fubarino/fubarino.github.com/images/FubarinoMiniLarge.jpg

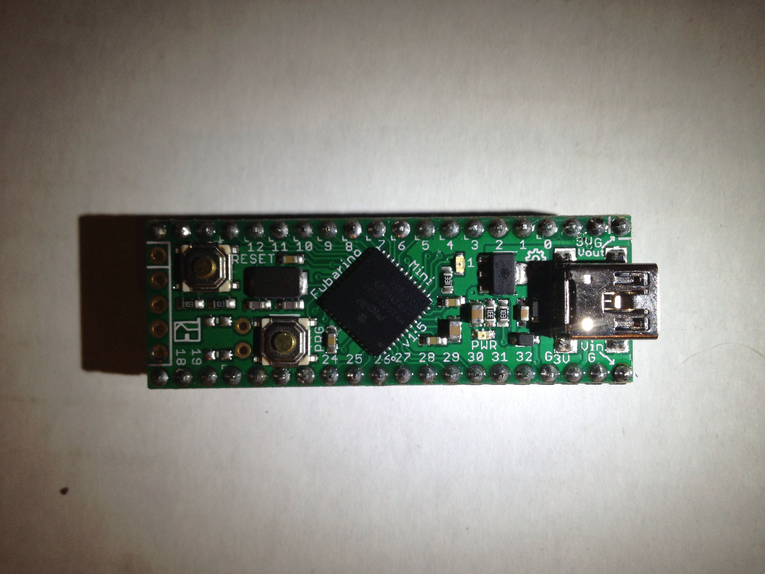
images/FubarinoMiniLarge.jpg
