fubarino/fubarino.github.com/images/FubarinoMiniMCHP.png

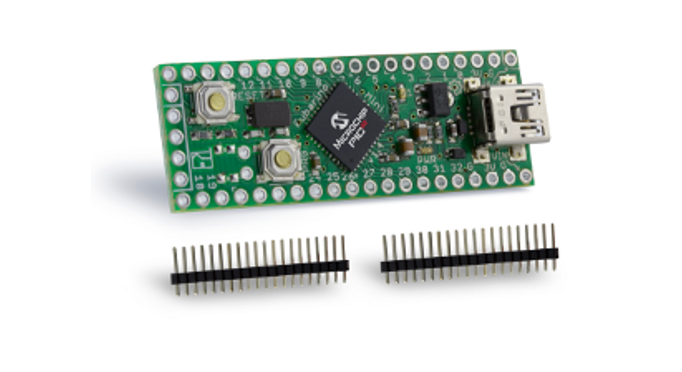
images/FubarinoMiniMCHP.png
