fubarino/fubarino.github.com/images/FubarinoMiniv15-caro-0.jpg

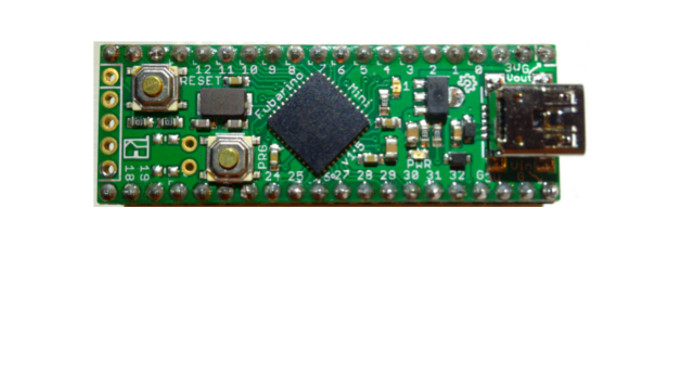
images/FubarinoMiniv15-caro-0.jpg
