fubarino/fubarino.github.com/images/FubarinoMiniv15-caro-1.jpg

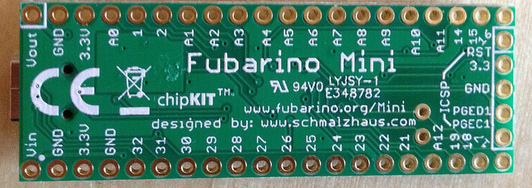
images/FubarinoMiniv15-caro-1.jpg
