fubarino/fubarino.github.com/images/FubarinoMiniv15-small.jpg

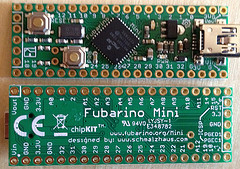
images/FubarinoMiniv15-small.jpg
