fubarino/fubarino.github.com/images/fubarinosd1.jpg

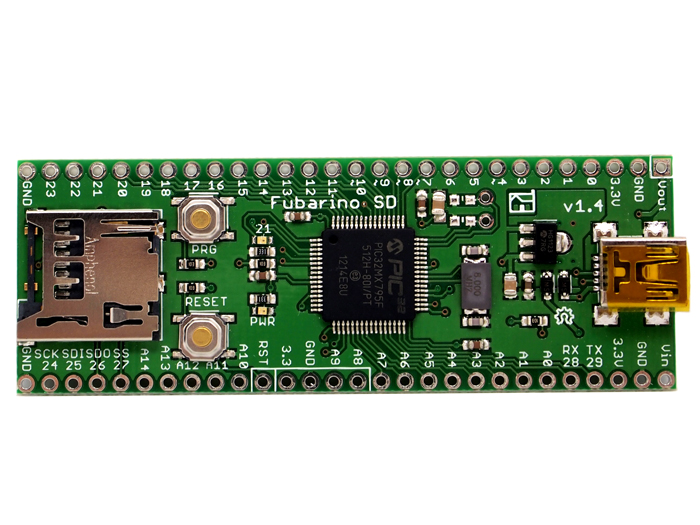
images/fubarinosd1.jpg
