fubarino/fubarino.github.com/images/fubarinosd1.png

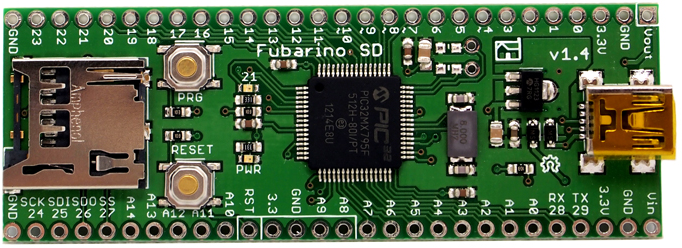
images/fubarinosd1.png
