fubarino/fubarino.github.com/images/fubarinosd2.jpg

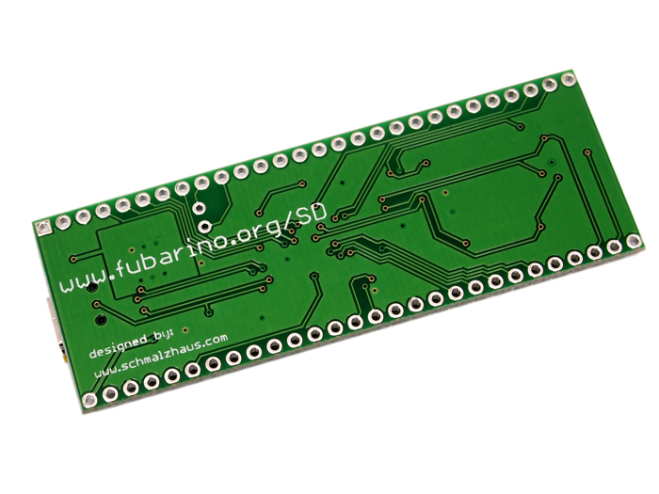
images/fubarinosd2.jpg
