fubarino/fubarino.github.com/images/fubarinosd-caro.jpg

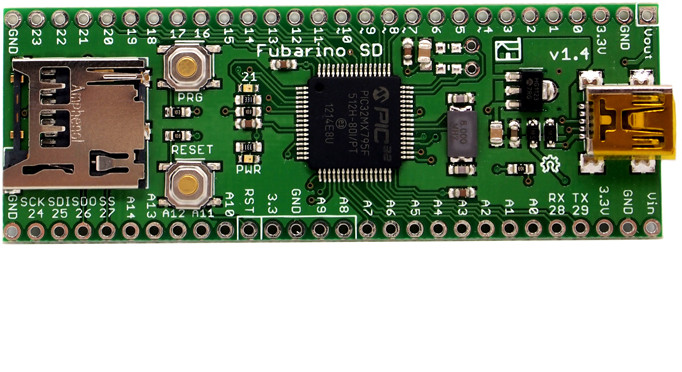
images/fubarinosd-caro.jpg
