fubarino/fubarino.github.com/images/fubarinosd.jpg

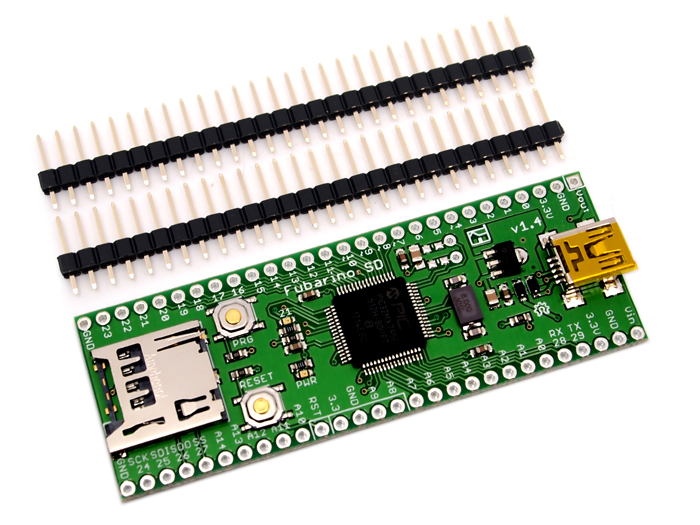
images/fubarinosd.jpg
