fubarino/fubarino.github.com/images/TCHIP011_chipKITFubarinoMini.png

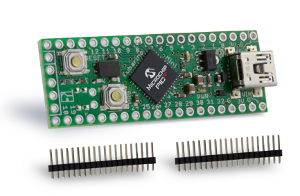
images/TCHIP011_chipKITFubarinoMini.png
