fubarino/fubarino.github.com/mini/docs/FubarinoMini1_5Diagram.png

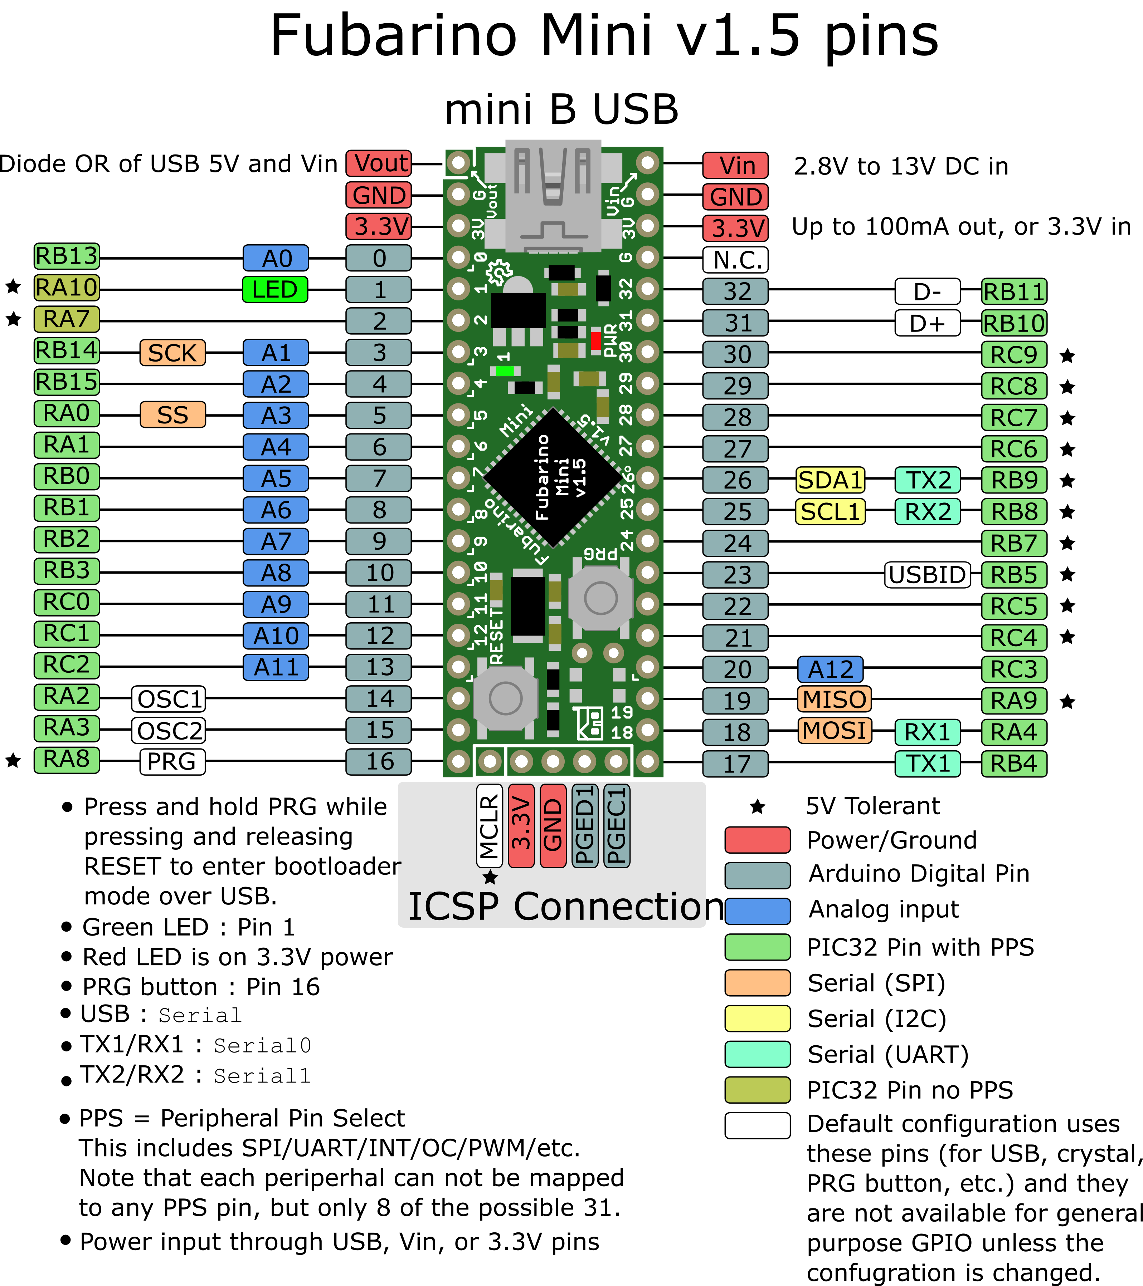
mini/docs/FubarinoMini1_5Diagram.png
