fubarino/fubarino.github.com/mini/fubarinoMini.png

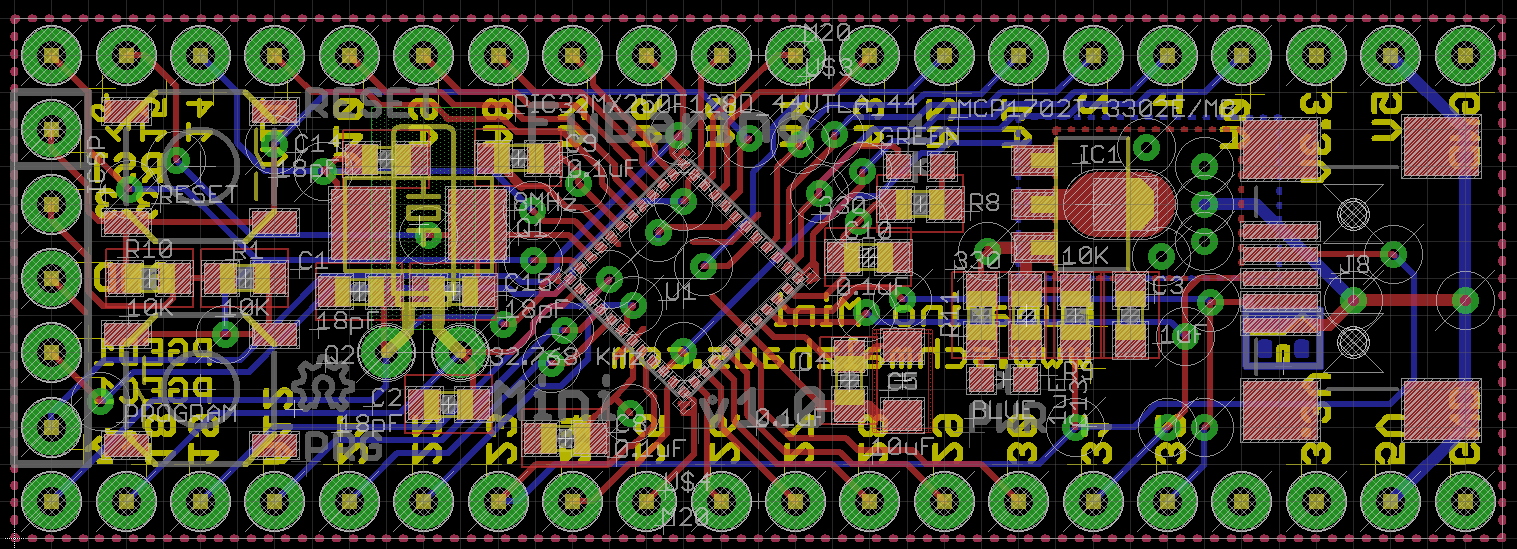
mini/fubarinoMini.png
