fubarino/fubarino.github.com/rawfiles/ProgrammingFubarino.jpg

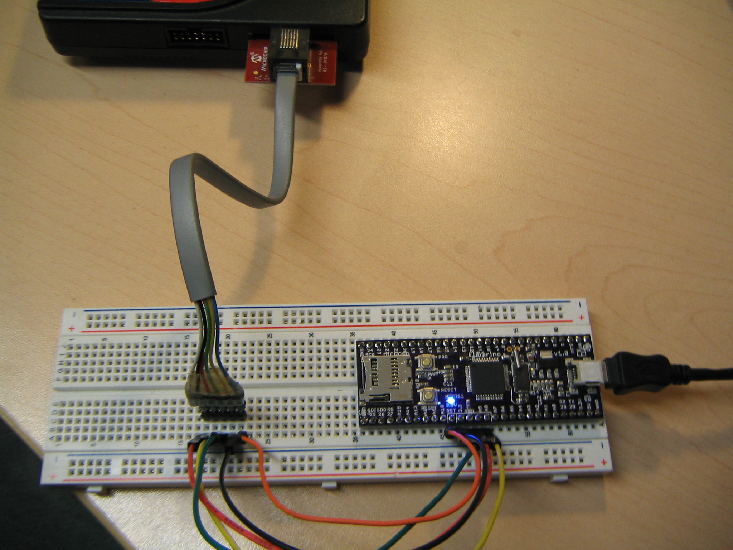
rawfiles/ProgrammingFubarino.jpg
