fubarino/fubarino.github.com/rawfiles/ShieldAdapterMockup.png

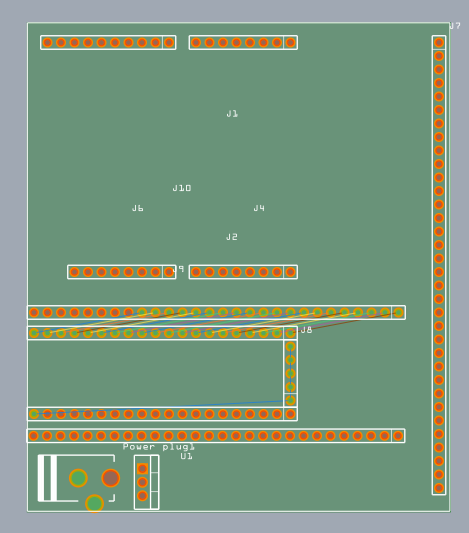
rawfiles/ShieldAdapterMockup.png
