fubarino/fubarino.github.com/rawfiles/shields/AdapterShield.png

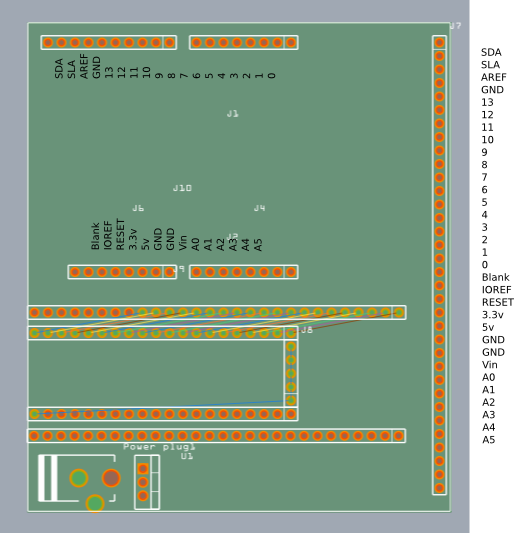
rawfiles/shields/AdapterShield.png
