fubarino/fubarino.github.com/sd/fubarinoSD.png

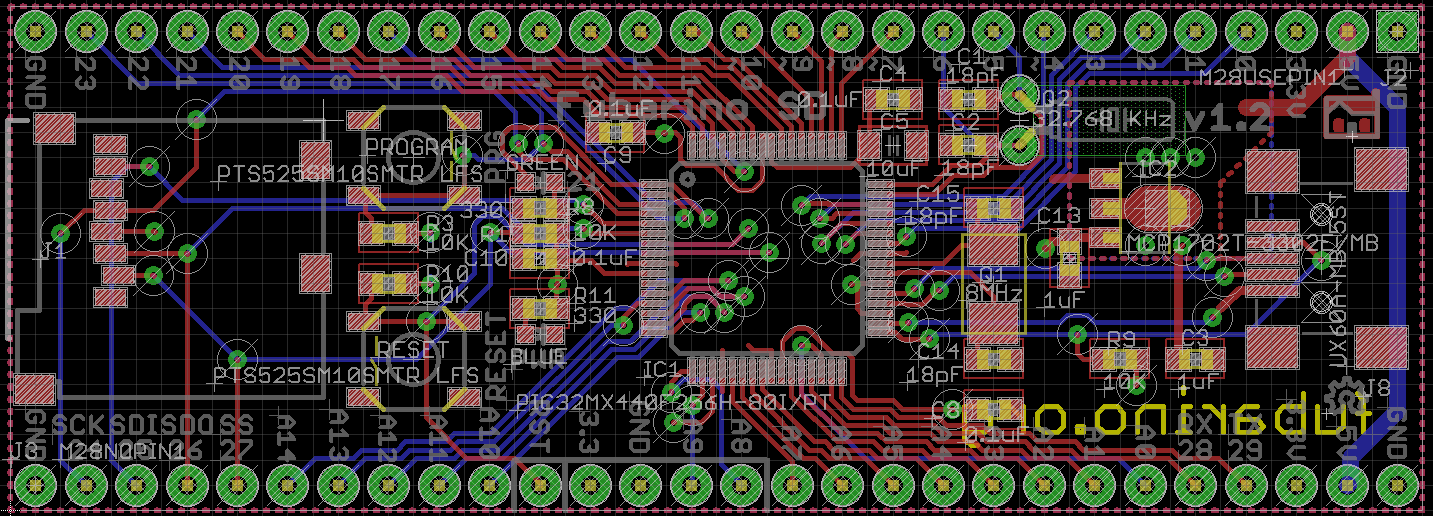
sd/fubarinoSD.png
