fubarino/fubarino.github.com/sd/v1.5/05-10133r15/Fubarino_SD_v15_DRC_screencap.png

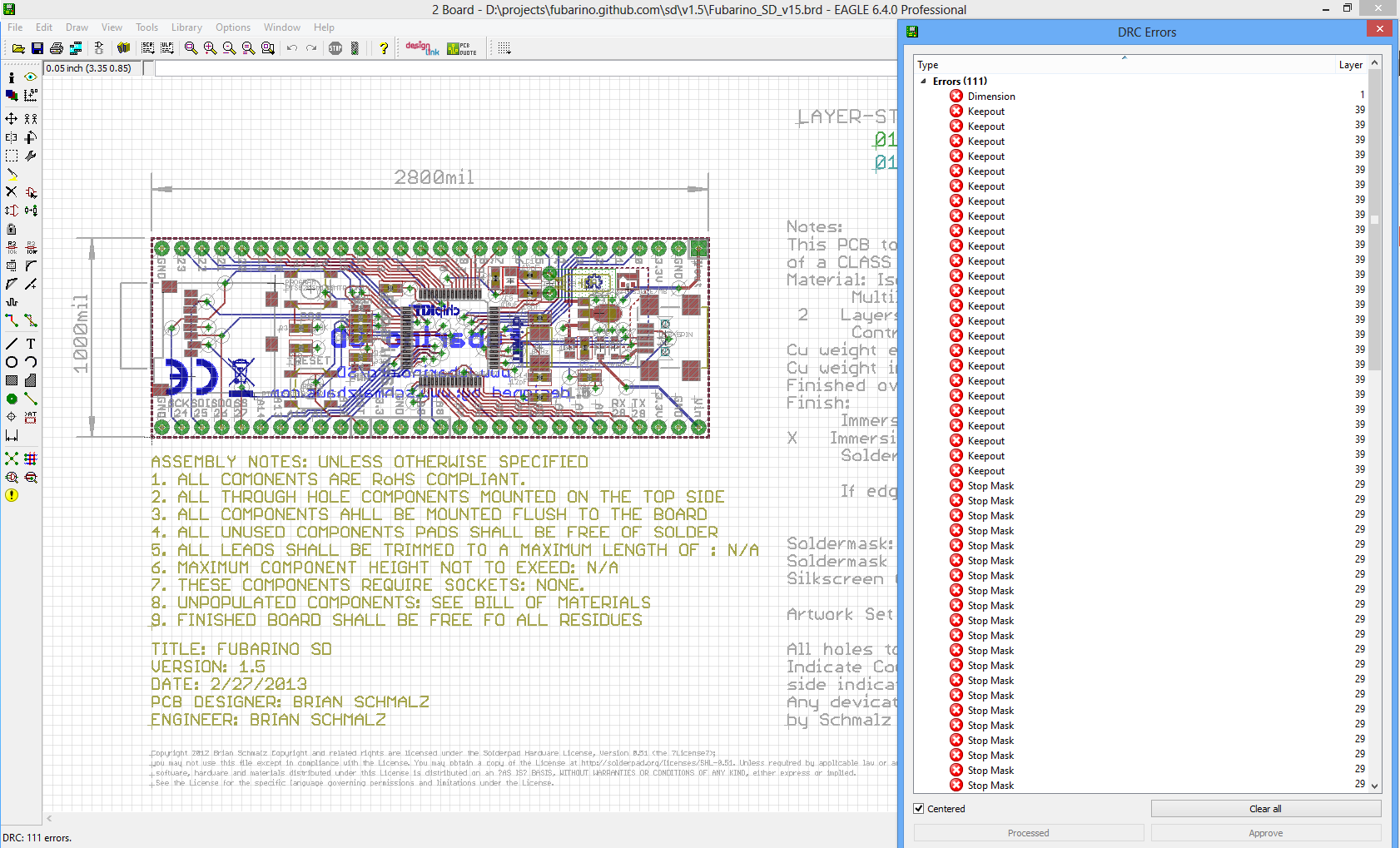
sd/v1.5/05-10133r15/Fubarino_SD_v15_DRC_screencap.png
