fubarino/fubarino.github.com/sd/v1.5/FubarinoSD_bottom_render.png

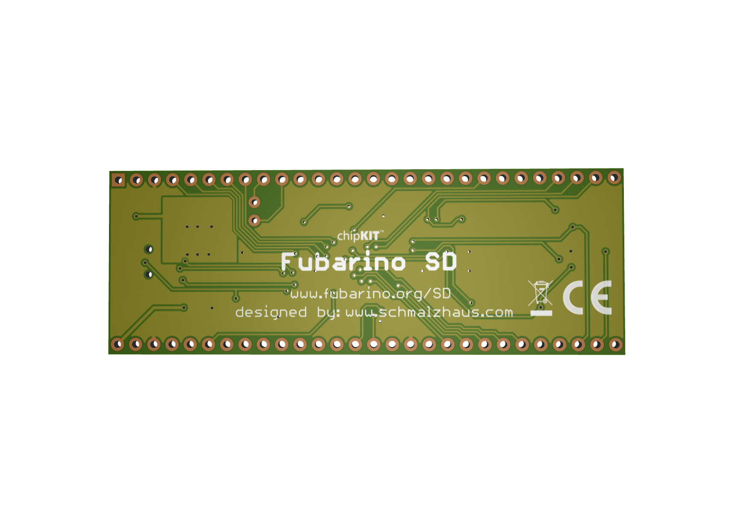
sd/v1.5/FubarinoSD_bottom_render.png
