fubarino/fubarino.github.com/accessories/FubarStep/FuabarStep_v13/FubarStep_v13_brd.png

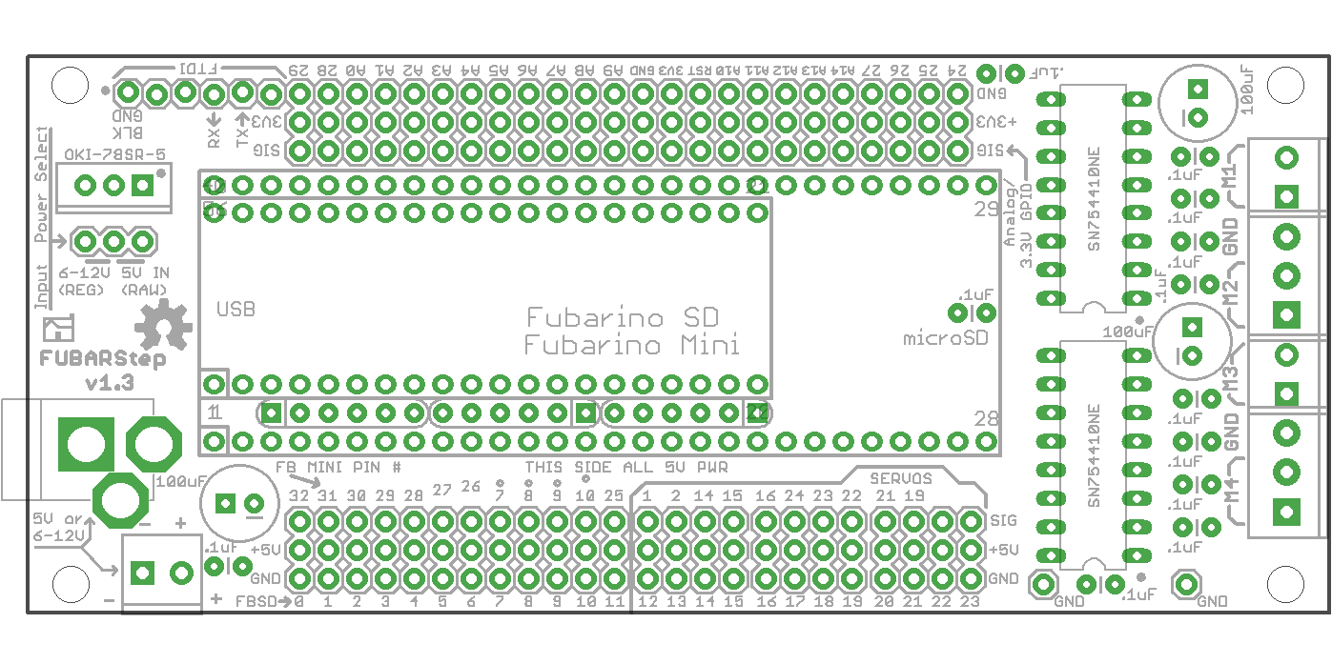
accessories/FubarStep/FuabarStep_v13/FubarStep_v13_brd.png
