fubarino/fubarino.github.com/accessories/FubarStep/FuabarStep_v13/FubarStep_v13_sch.pdf

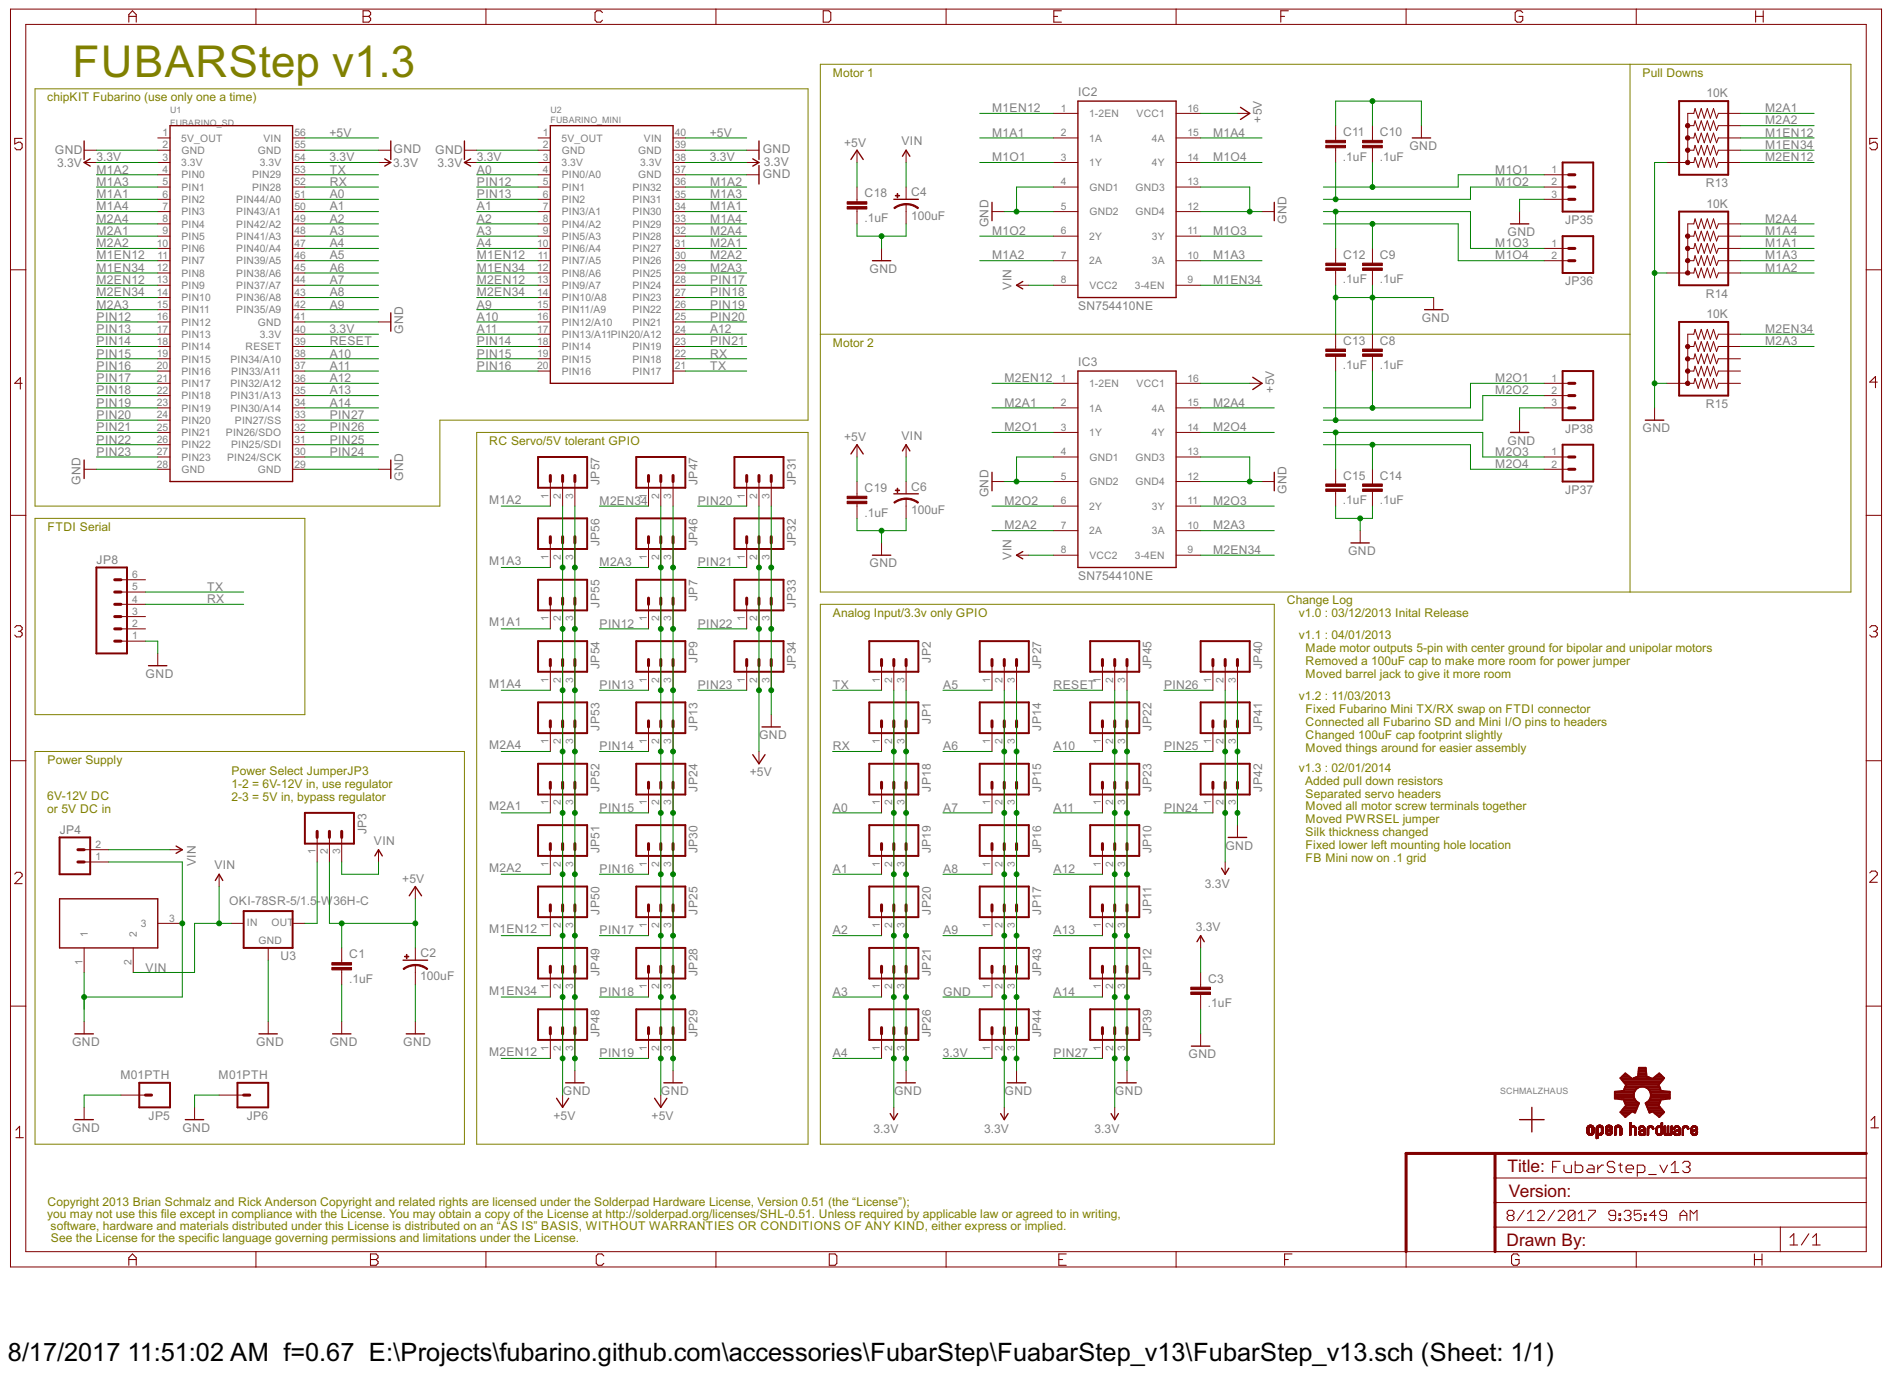
[picture p30: page 1]

chipKIT Fubarino (use only one a time)

RC Servo/5V tolerant GPIO

Analog Input/3.3v only GPIO

v1.1 : 04/01/2013 Made motor outputs 5-pin with center ground for bipolar and unipolar motors Removed a 100uF cap to make more room for power jumper Moved barrel jack to give it more room

v1.2 : 11/03/2013 Fixed Fubarino Mini TX/RX swap on FTDI connector Connected all Fubarino SD and Mini I/O pins to headers Changed 100uF cap footprint slightly Moved things around for easier assembly

Power Select JumperJP3
1-2 = 6V-12V in, use regulator 2-3 = 5V in, bypass regulator

v1.3 : 02/01/2014 Added pull down resistors Separated servo headers Moved all motor screw terminals together Moved PWRSEL jumper Silk thickness changed Fixed lower left mounting hole location FB Mini now on .1 grid

Drawn By: Title: Version:

Copyright 2013 Brian Schmalz and Rick Anderson Copyright and related rights are licensed under the Solderpad Hardware License, Version 0.51 (the “License”); you may not use this file except in compliance with the License. You may obtain a copy of the License at http://solderpad.org/licenses/SHL-0.51. Unless required by applicable law or agreed to in writing, software, hardware and materials distributed under this License is distributed on an “AS IS” BASIS, WITHOUT WARRANTIES OR CONDITIONS OF ANY KIND, either express or implied. See the License for the specific language governing permissions and limitations under the License.

8/17/2017 11:51:02 AM f=0.67 E:\Projects\fubarino.github.com\accessories\FubarStep\FuabarStep_v13\FubarStep_v13.sch (Sheet: 1/1)
