fubarino/fubarino.github.com/mini/v20/02-10134r20-D.pdf

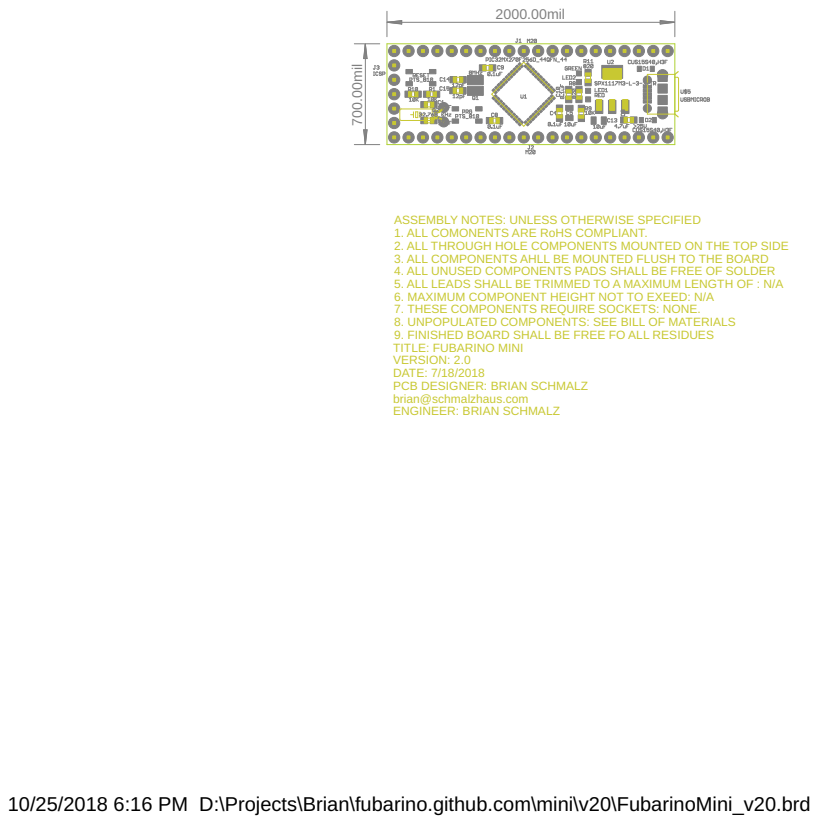
[picture p31: page 1]

ASSEMBLY NOTES: UNLESS OTHERWISE SPECIFIED
1. ALL COMONENTS ARE RoHS COMPLIANT. 2. ALL THROUGH HOLE COMPONENTS MOUNTED ON THE TOP SIDE

3. ALL COMPONENTS AHLL BE MOUNTED FLUSH TO THE BOARD
4. ALL UNUSED COMPONENTS PADS SHALL BE FREE OF SOLDER
5. ALL LEADS SHALL BE TRIMMED TO A MAXIMUM LENGTH OF : N/A
6. MAXIMUM COMPONENT HEIGHT NOT TO EXEED: N/A
7. THESE COMPONENTS REQUIRE SOCKETS: NONE. 8. UNPOPULATED COMPONENTS: SEE BILL OF MATERIALS

9. FINISHED BOARD SHALL BE FREE FO ALL RESIDUES
TITLE: FUBARINO MINI VERSION: 2.0 DATE: 7/18/2018 PCB DESIGNER: BRIAN SCHMALZ

10/25/2018 6:16 PM D:\Projects\Brian\fubarino.github.com\mini\v20\FubarinoMini_v20.brd
