fubarino/fubarino.github.com/mini/v20/04-10134r20.pdf

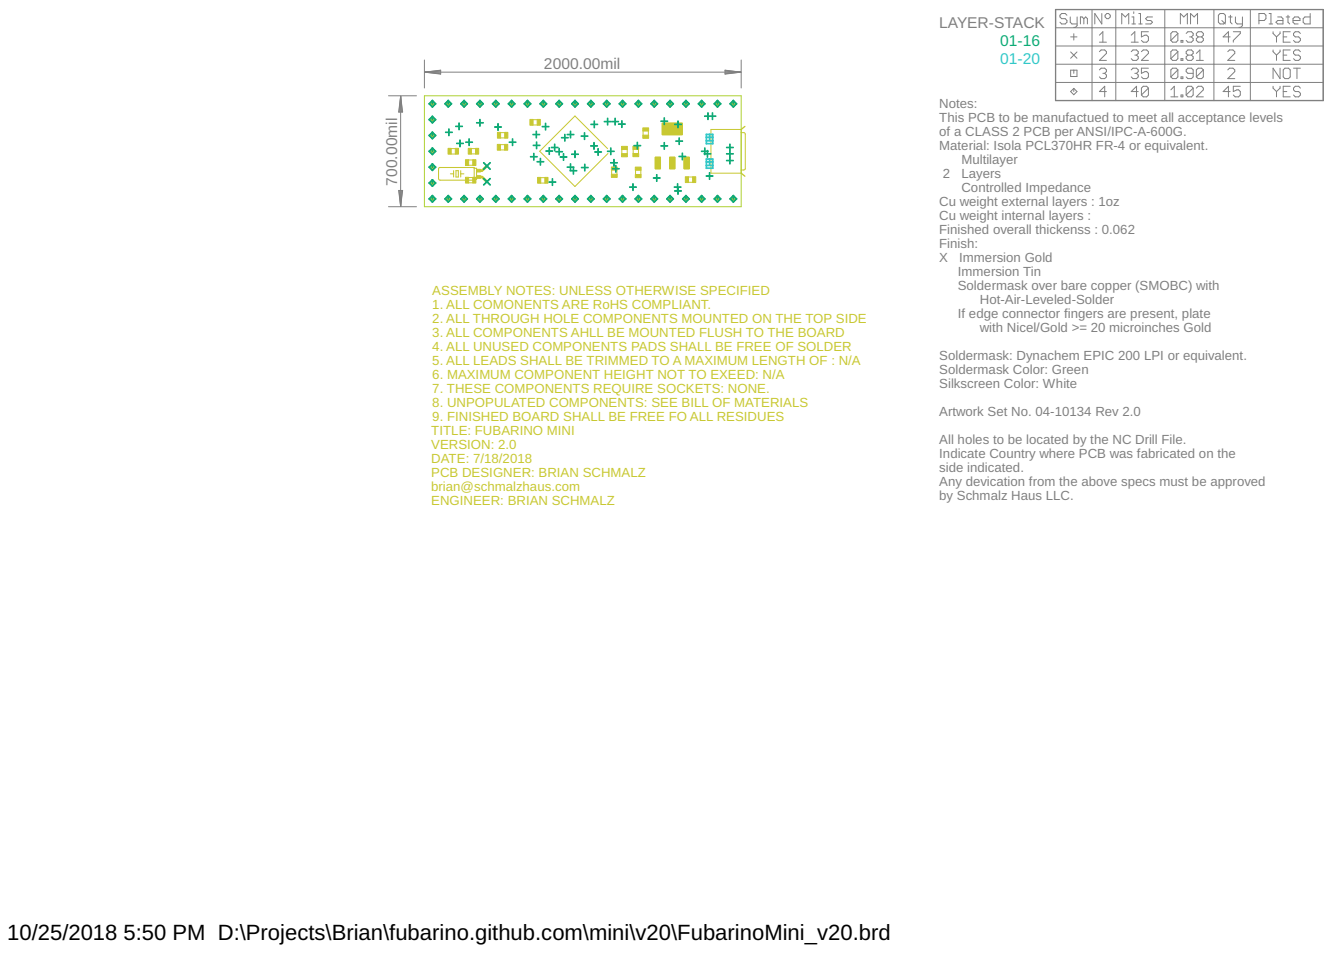
[picture p32: page 1]

01-20 Notes: This PCB to be manufactued to meet all acceptance levels of a CLASS 2 PCB per ANSI/IPC-A-600G. Material: Isola PCL370HR FR-4 or equivalent. Multilayer 2 Layers Controlled Impedance Cu weight external layers : 1oz Cu weight internal layers : Finished overall thickenss : 0.062 Finish: X Immersion Gold

Immersion Tin Soldermask over bare copper (SMOBC) with Hot-Air-Leveled-Solder

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

If edge connector fingers are present, plate with Nicel/Gold >= 20 microinches Gold Soldermask: Dynachem EPIC 200 LPI or equivalent. Soldermask Color: Green Silkscreen Color: White Artwork Set No. 04-10134 Rev 2.0 All holes to be located by the NC Drill File.

3. ALL COMPONENTS AHLL BE MOUNTED FLUSH TO THE BOARD
4. ALL UNUSED COMPONENTS PADS SHALL BE FREE OF SOLDER
5. ALL LEADS SHALL BE TRIMMED TO A MAXIMUM LENGTH OF : N/A
6. MAXIMUM COMPONENT HEIGHT NOT TO EXEED: N/A
7. THESE COMPONENTS REQUIRE SOCKETS: NONE. 8. UNPOPULATED COMPONENTS: SEE BILL OF MATERIALS

9. FINISHED BOARD SHALL BE FREE FO ALL RESIDUES
TITLE: FUBARINO MINI VERSION: 2.0 DATE: 7/18/2018 PCB DESIGNER: BRIAN SCHMALZ

Indicate Country where PCB was fabricated on the
side indicated. Any devication from the above specs must be approved

by Schmalz Haus LLC.

10/25/2018 5:50 PM D:\Projects\Brian\fubarino.github.com\mini\v20\FubarinoMini_v20.brd
