fubarino/fubarino.github.com/mini/docs/FubarinoMiniDiagram.pdf

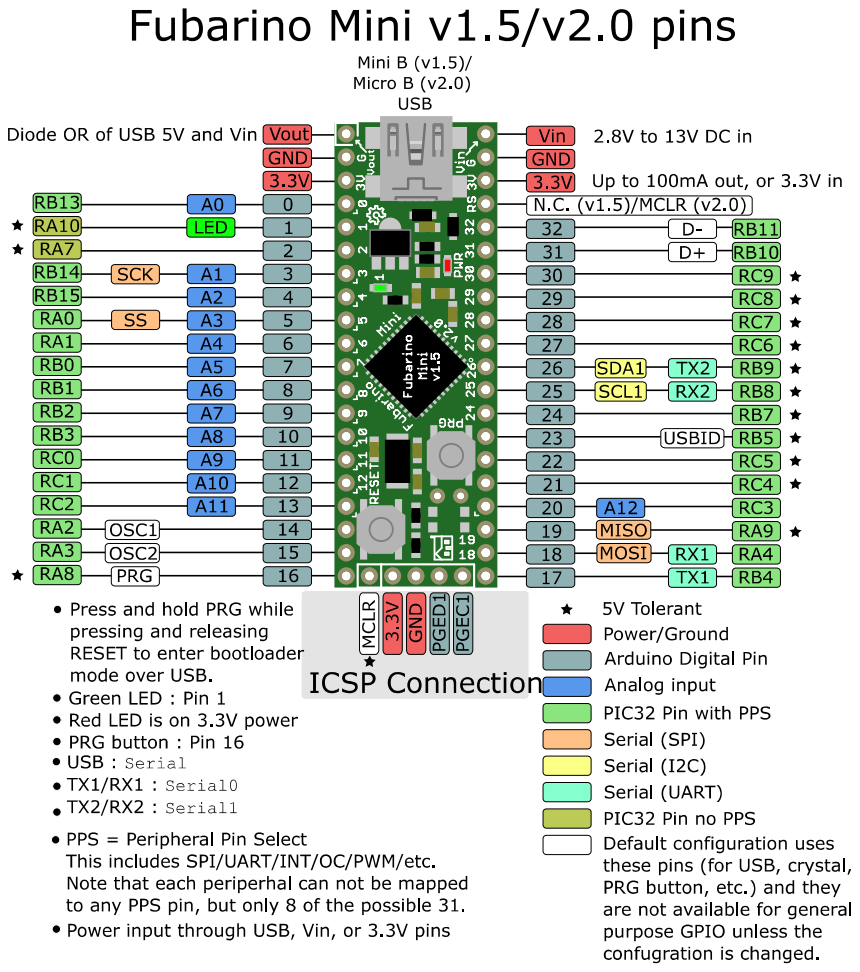
[picture p39: page 1]
