fubarino/fubarino.github.com/mini/docs/FubarinoMini1_5Diagram.pdf

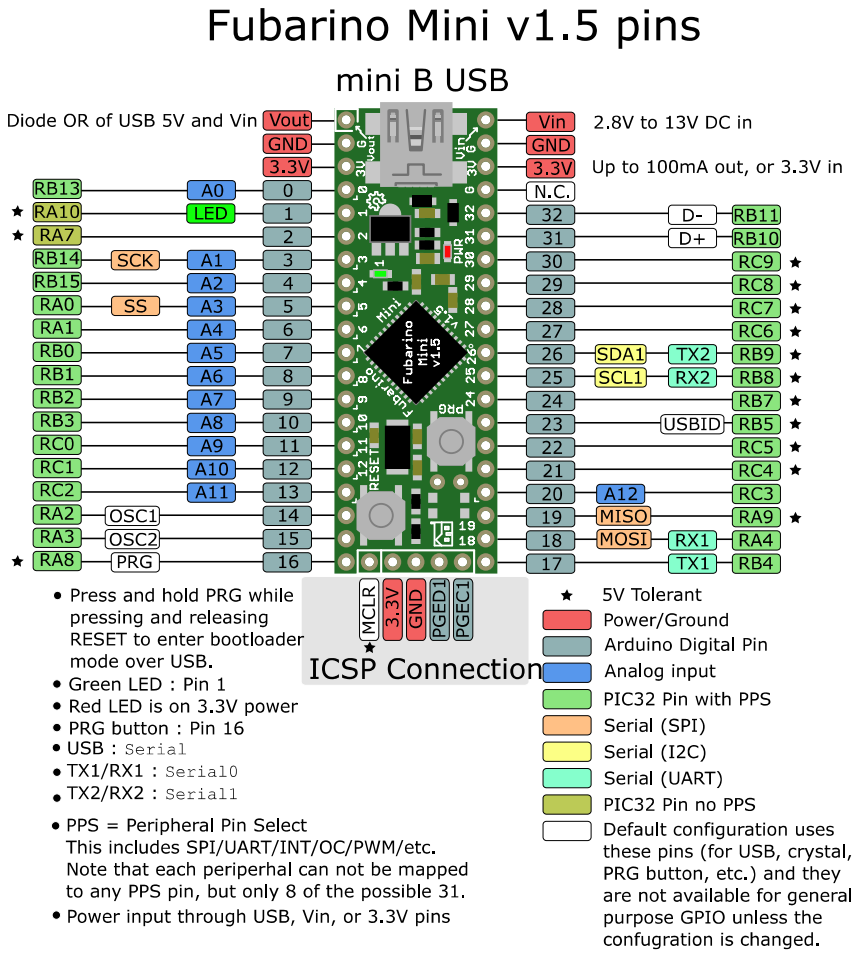
[picture p40: page 1]
