fubarino/fubarino.github.com/mini/docs/FubarinoMini2_0Diagram.pdf

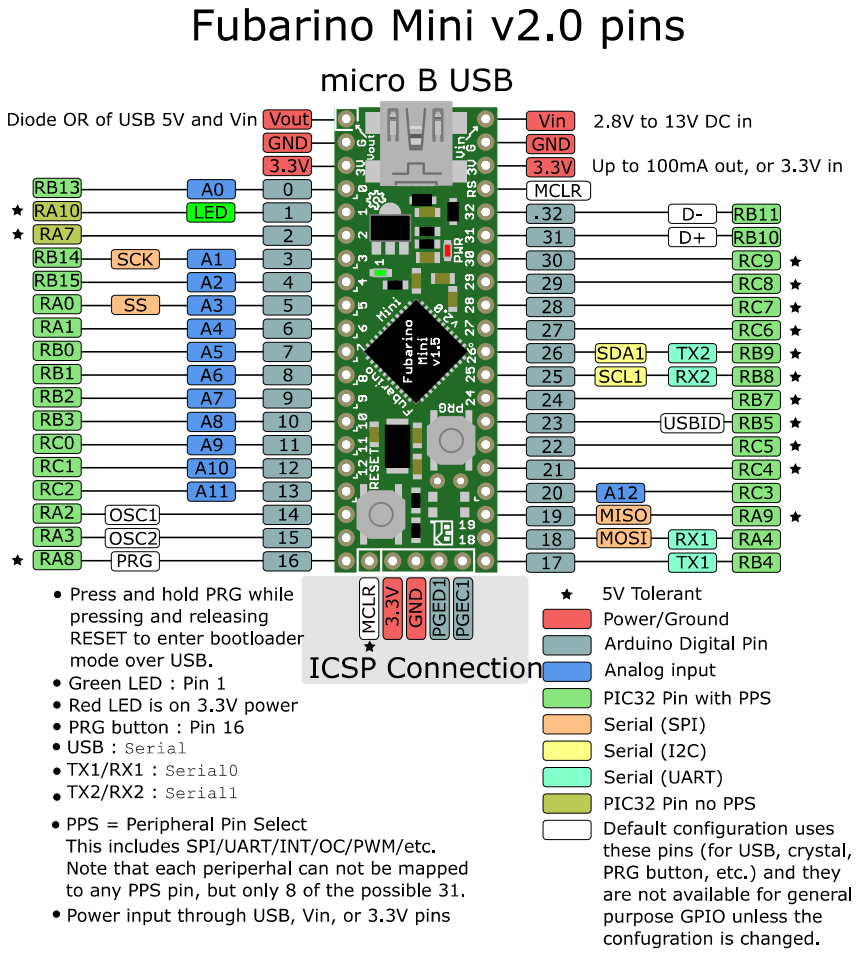
[picture p41: page 1]
