fubarino/fubarino.github.com/projects/FBMiniProto/FBMiniProto_brd.pdf

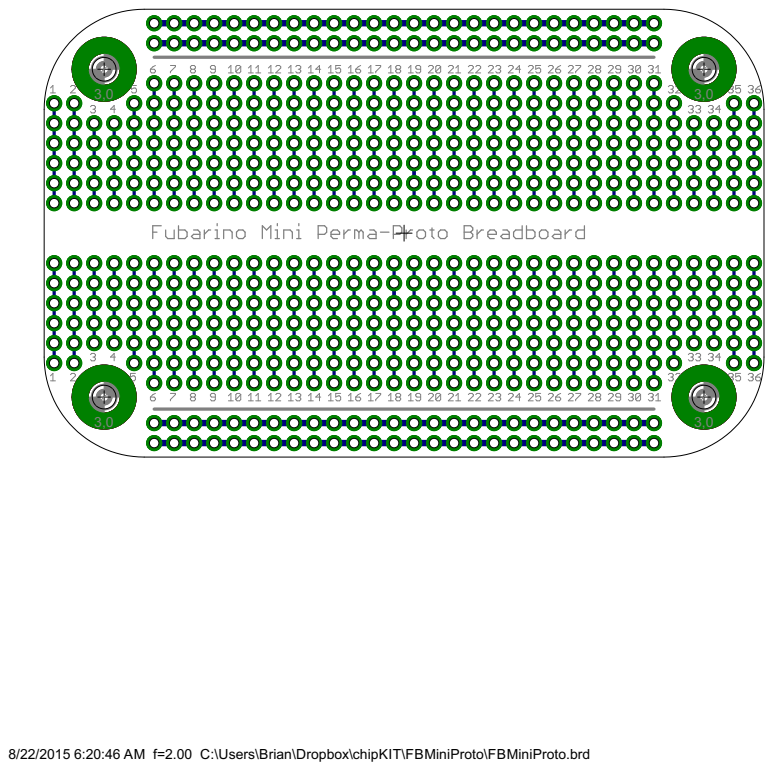
[picture p42: page 1]

8/22/2015 6:20:46 AM f=2.00 C:\Users\Brian\Dropbox\chipKIT\FBMiniProto\FBMiniProto.brd
