fubarino/fubarino.github.com/sd/v1.5/03-10133r15.pdf

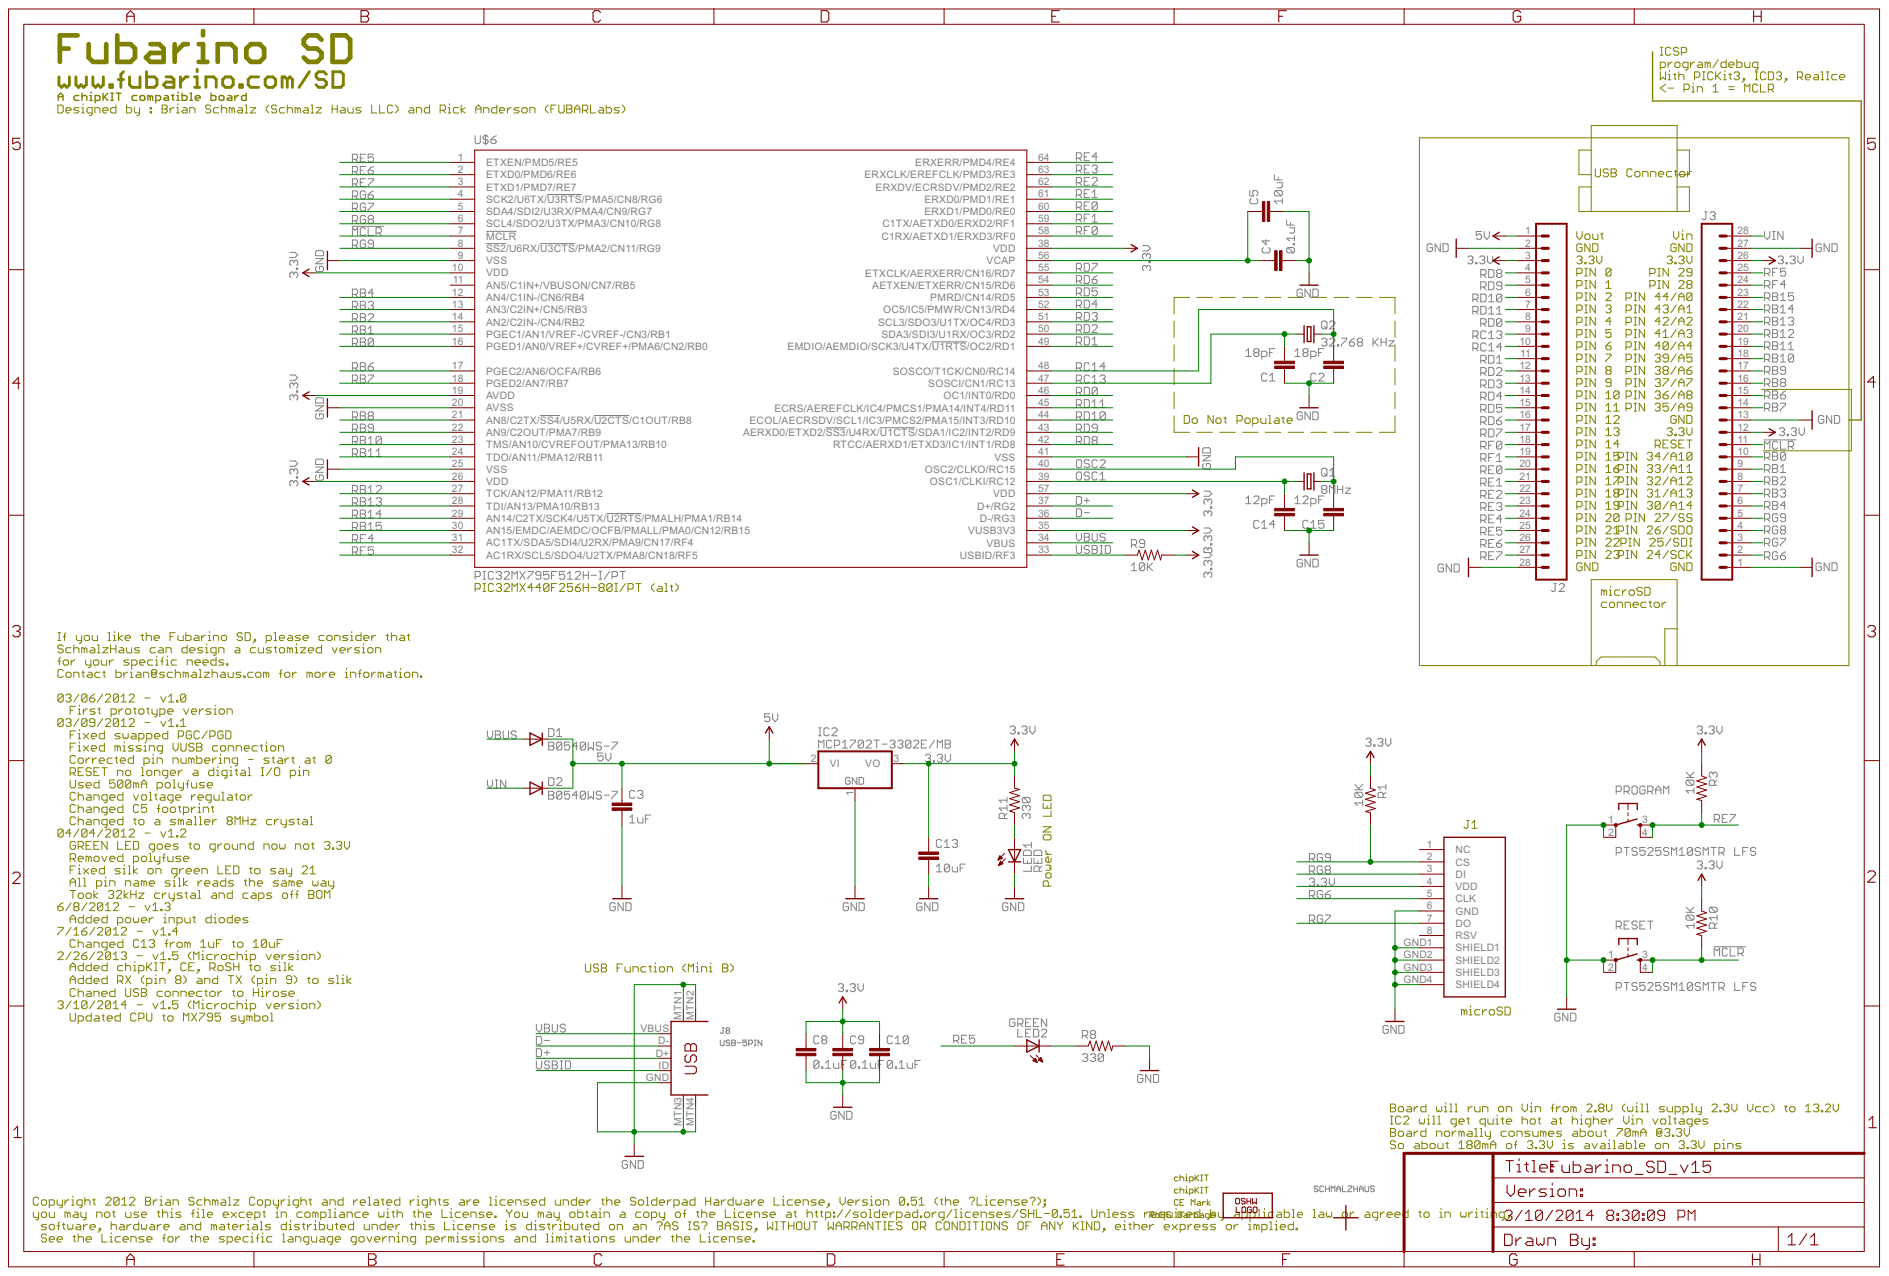
[picture p43: page 1]
