fubarino/fubarino.github.com/sd/v1.5/04-10133r15.pdf

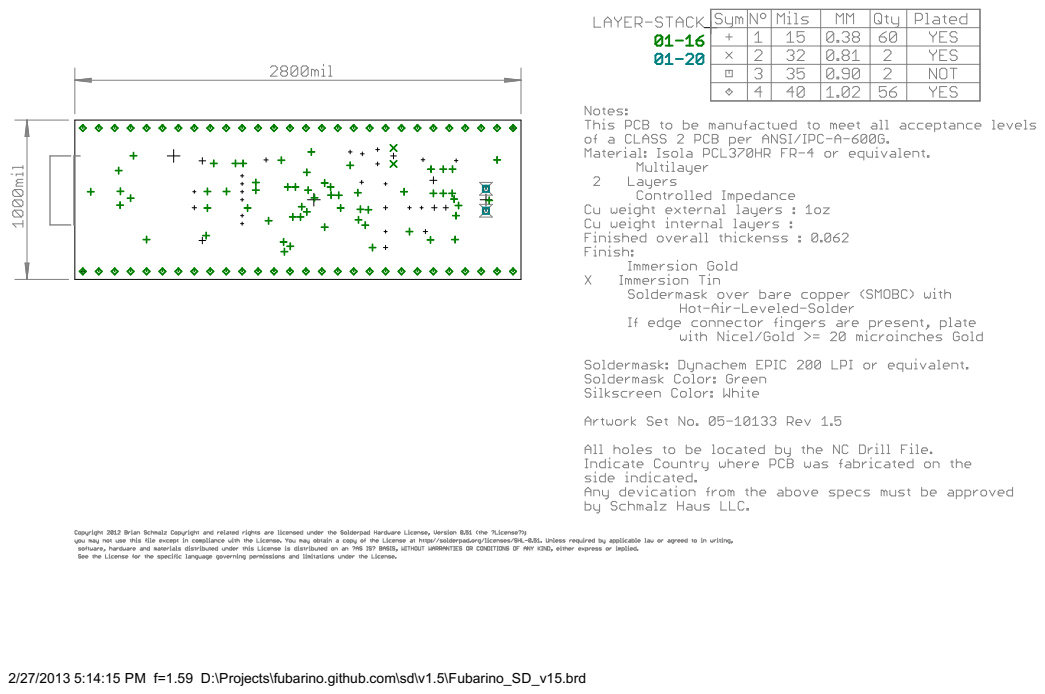
[picture p44: page 1]

2/27/2013 5:14:15 PM f=1.59 D:\Projects\fubarino.github.com\sd\v1.5\Fubarino_SD_v15.brd
