fubarino/fubarino.github.com/sd/v1.5/Fubarino_SD_v15_brd.pdf

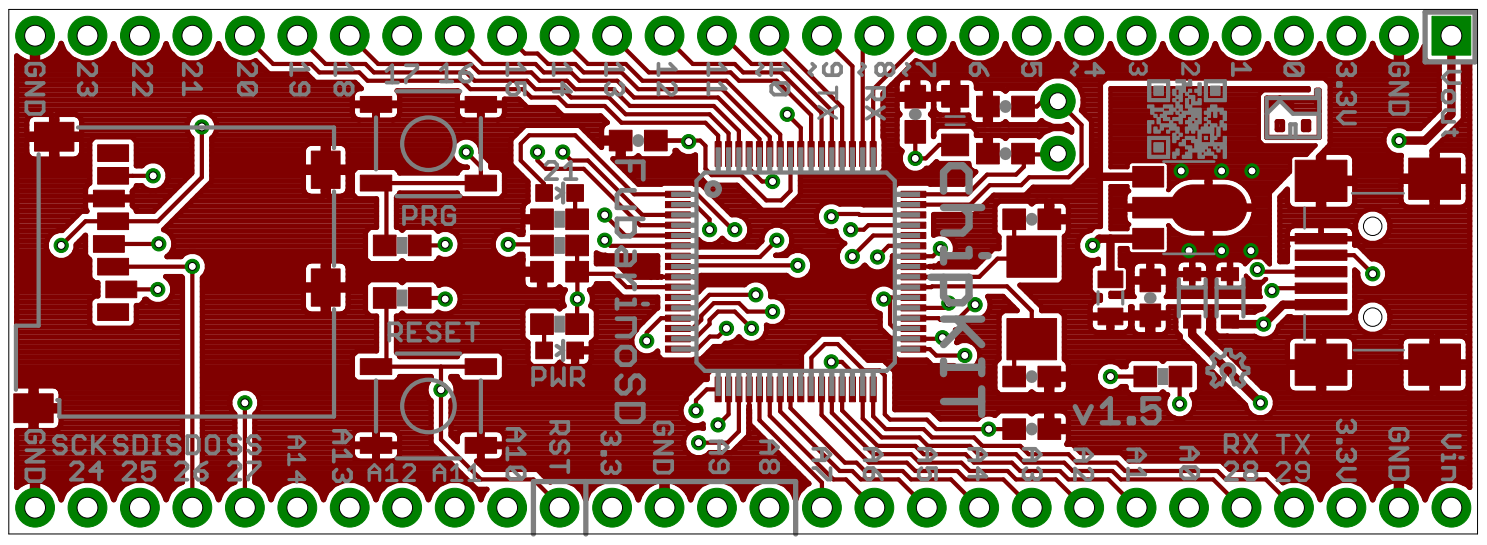
[picture p45: page 1]
