fubarino/fubarino.github.com/sd/v1.4/Fubarino_SD_v14_sch.pdf

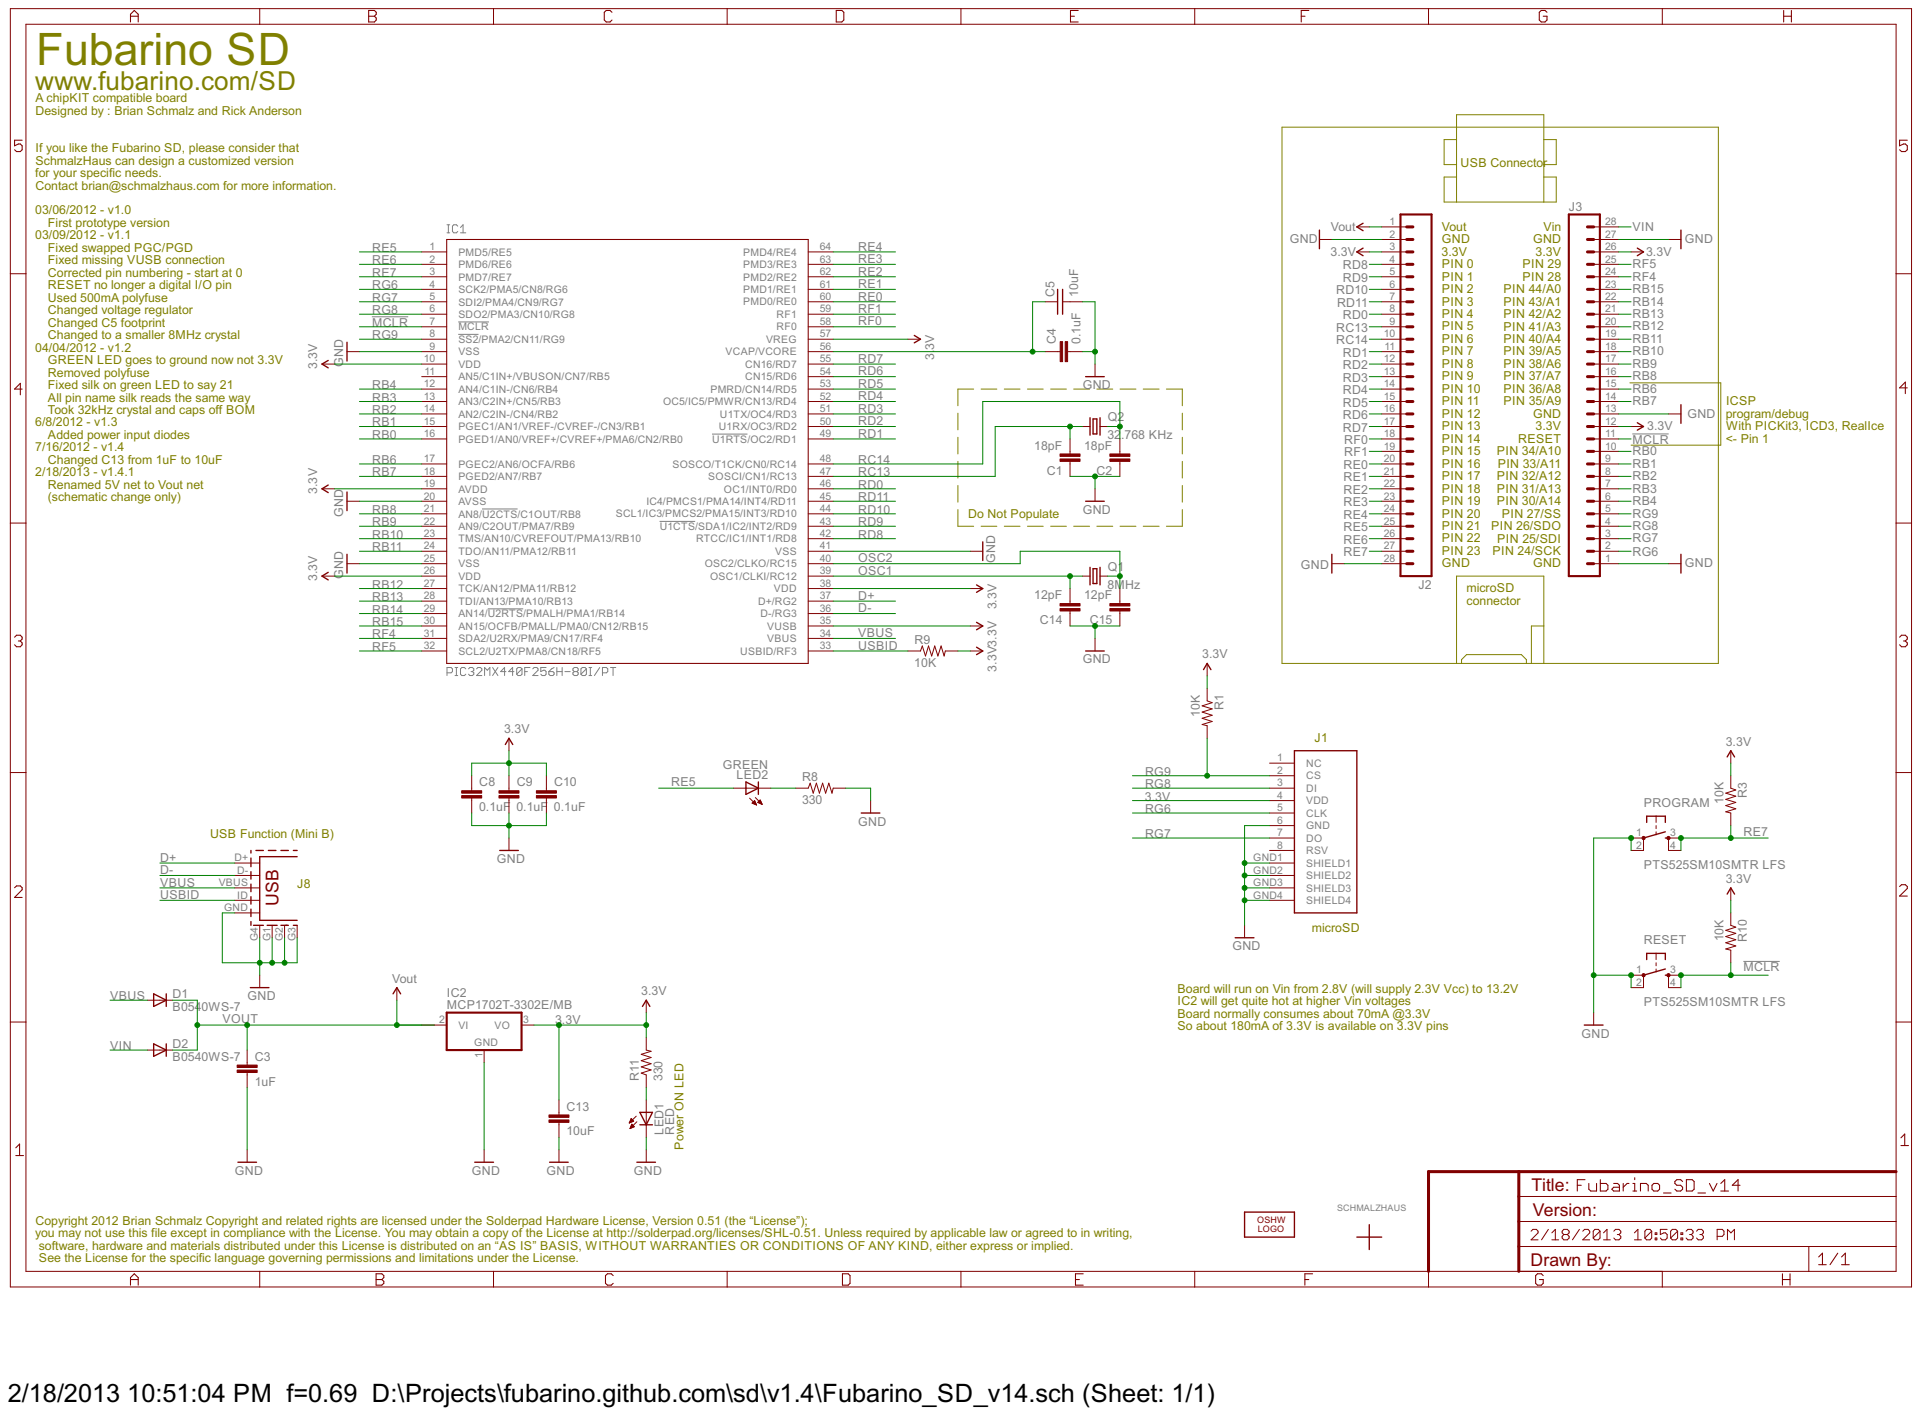
[picture p46: page 1]

Fubarino SD
www.fubarino.com/SD

A chipKIT compatible board
Designed by : Brian Schmalz and Rick Anderson

If you like the Fubarino SD, please consider that SchmalzHaus can design a customized version

USB Connector
PIN 35/A9 PIN 36/A8 PIN 37/A7 PIN 38/A6 PIN 39/A5 PIN 40/A4 PIN 41/A3 PIN 42/A2 PIN 43/A1 PIN 44/A0 PIN 28 PIN 29

03/09/2012 - v1.1 Fixed swapped PGC/PGD

Fixed missing VUSB connection Corrected pin numbering - start at 0 RESET no longer a digital I/O pin Used 500mA polyfuse Changed voltage regulator Changed C5 footprint Changed to a smaller 8MHz crystal

04/04/2012 - v1.2 GREEN LED goes to ground now not 3.3V Removed polyfuse Fixed silk on green LED to say 21 All pin name silk reads the same way

Took 32kHz crystal and caps off BOM
6/8/2012 - v1.3 Added power input diodes

ICSP
program/debug With PICKit3, ICD3, RealIce <- Pin 1

PIN 30/A14 PIN 31/A13 PIN 32/A12 PIN 33/A11 PIN 34/A10 RESET

PIN 27/SS
PIN 25/SDI PIN 26/SDO

Board will run on Vin from 2.8V (will supply 2.3V Vcc) to 13.2V
IC2 will get quite hot at higher Vin voltages Board normally consumes about 70mA @3.3V

So about 180mA of 3.3V is available on 3.3V pins

Drawn By: Title: Version:

Copyright 2012 Brian Schmalz Copyright and related rights are licensed under the Solderpad Hardware License, Version 0.51 (the “License”); you may not use this file except in compliance with the License. You may obtain a copy of the License at http://solderpad.org/licenses/SHL-0.51. Unless required by applicable law or agreed to in writing, software, hardware and materials distributed under this License is distributed on an “AS IS” BASIS, WITHOUT WARRANTIES OR CONDITIONS OF ANY KIND, either express or implied. See the License for the specific language governing permissions and limitations under the License.

2/18/2013 10:51:04 PM f=0.69 D:\Projects\fubarino.github.com\sd\v1.4\Fubarino_SD_v14.sch (Sheet: 1/1)
