fubarino/fubarino.github.com/mini/v11/FubarinoMini_v11_sch.pdf

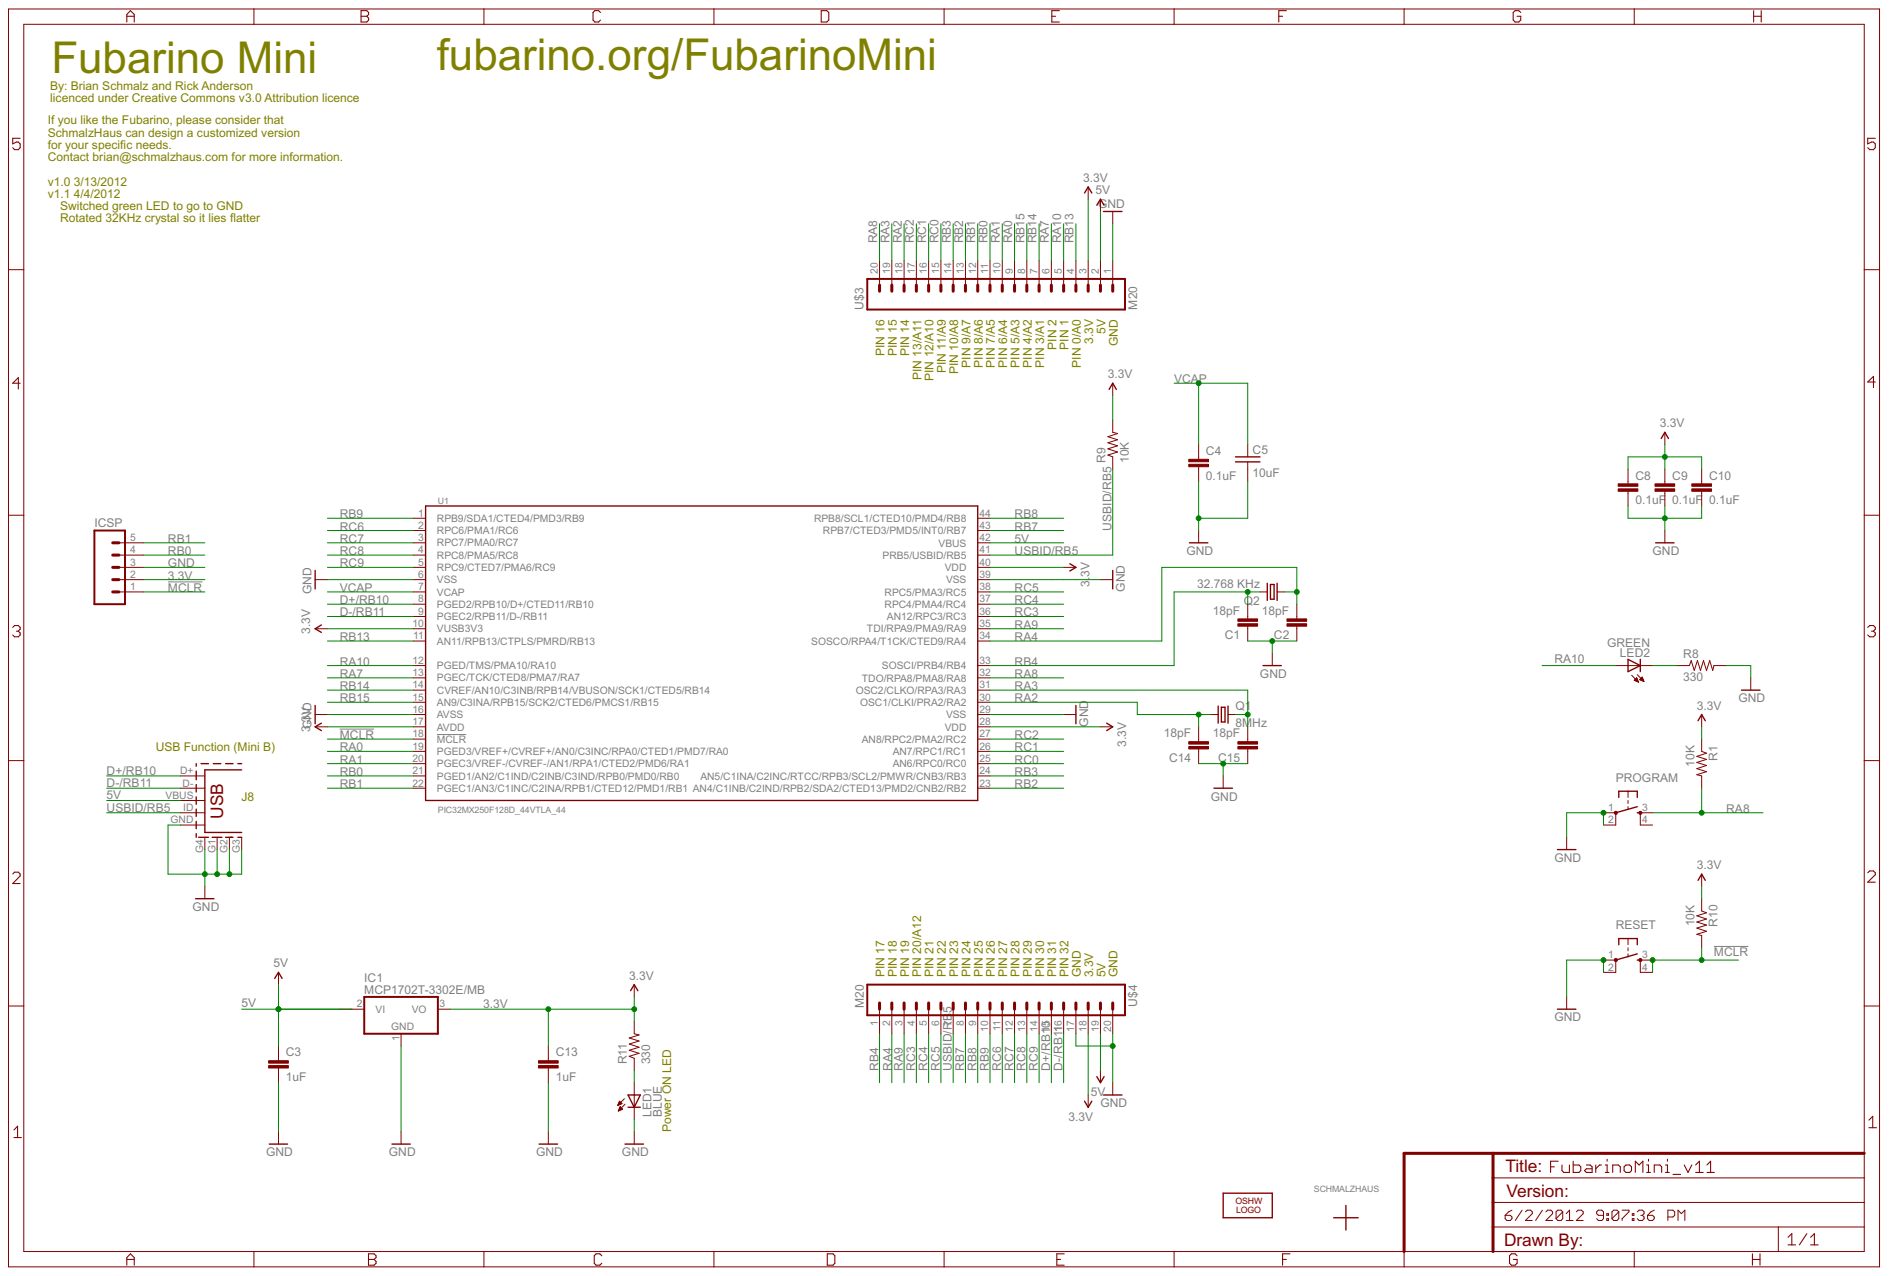
[picture p47: page 1]

By: Brian Schmalz and Rick Anderson
licenced under Creative Commons v3.0 Attribution licence

If you like the Fubarino, please consider that SchmalzHaus can design a customized version

for your specific needs. Contact brian@schmalzhaus.com for more information.

v1.1 4/4/2012 Switched green LED to go to GND

Rotated 32KHz crystal so it lies flatter

PIN 0/A0 PIN 1 PIN 2 PIN 3/A1 PIN 4/A2 PIN 5/A3 PIN 6/A4 PIN 7/A5 PIN 8/A6 PIN 9/A7 PIN 10/A8 PIN 11/A9 PIN 12/A10 PIN 13/A11 PIN 14 PIN 15 PIN 16 PIN 17 PIN 18 PIN 19 PIN 20/A12 PIN 21 PIN 22 PIN 23 PIN 24 PIN 25 PIN 26 PIN 27 PIN 28 PIN 29 PIN 30 PIN 31 PIN 32

Drawn By: Title: Version:
