fubarino/fubarino.github.com/mini/v16/FromMicrochip/04-10064/04-10064/03-10064r1.pdf

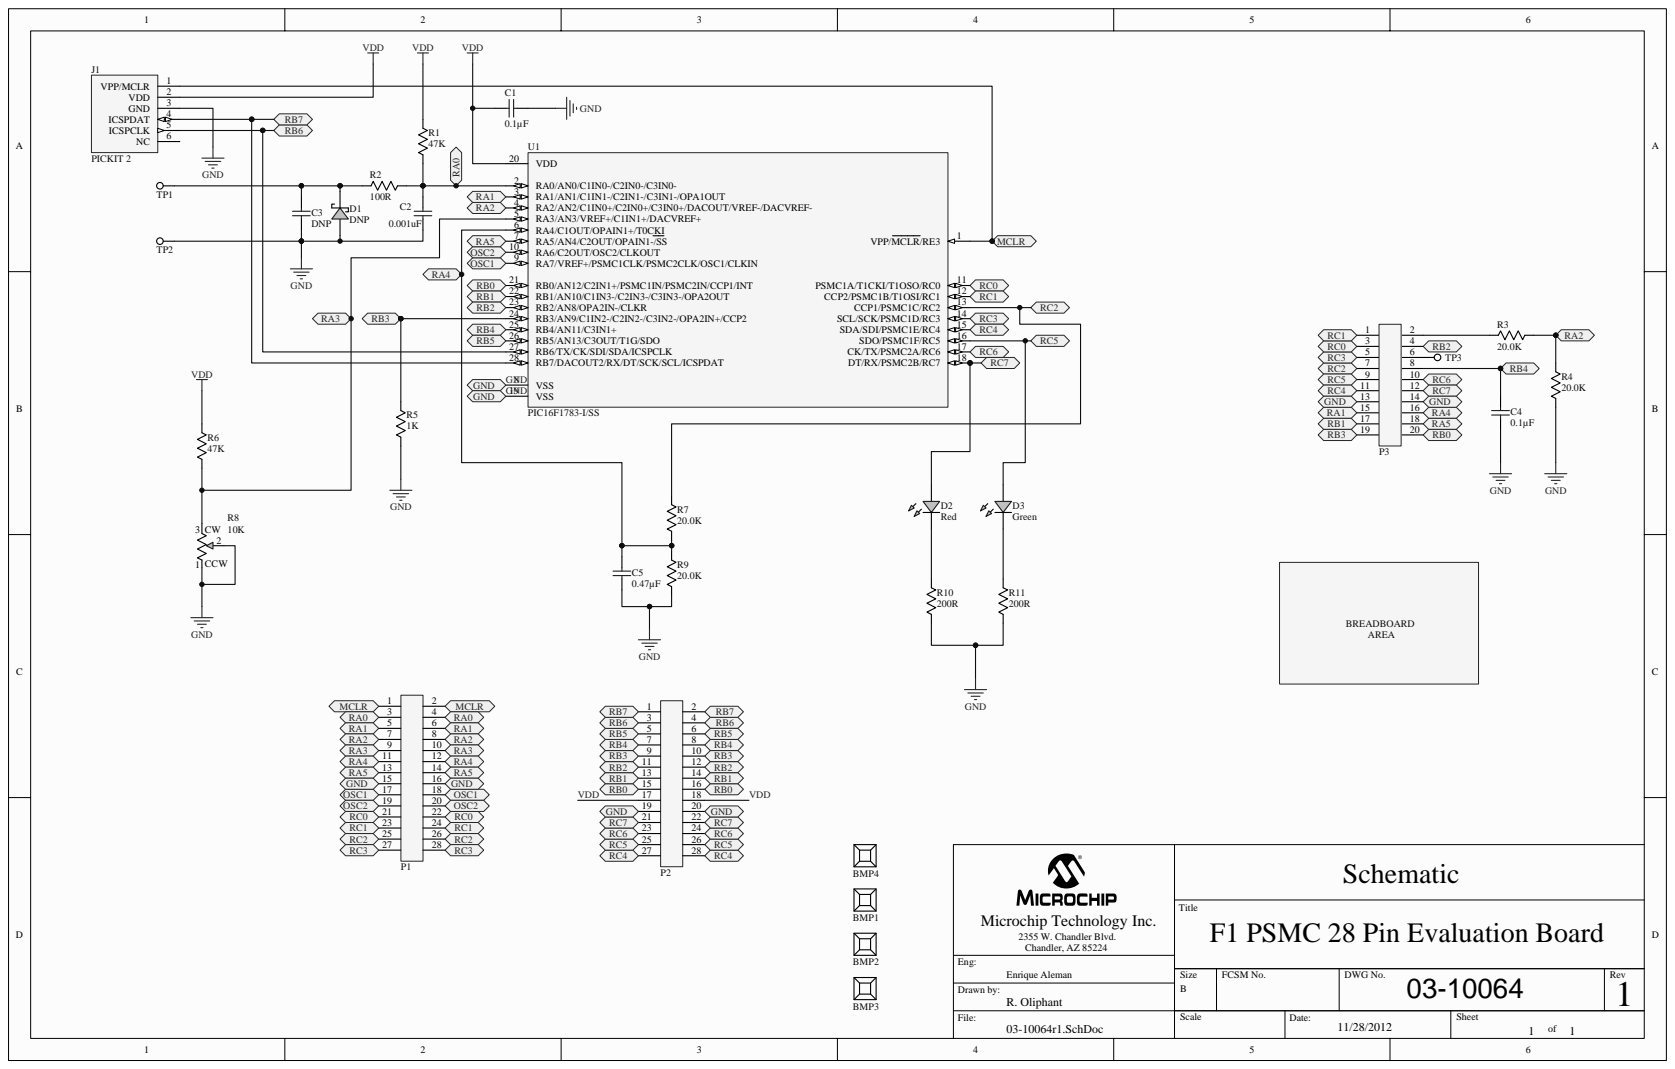
[picture p48: page 1]

VDD | VDD

Title
F1 PSMC 28 Pin Evaluation Board

Size B | FCSM No. | DWG No. 03-10064 | Rev 1

File: 03-10064r1.SchDoc | Scale | Date: 11/28/2012 | Sheet of 1 1
