fubarino/fubarino.github.com/mini/v16/02-10134r16-D.pdf

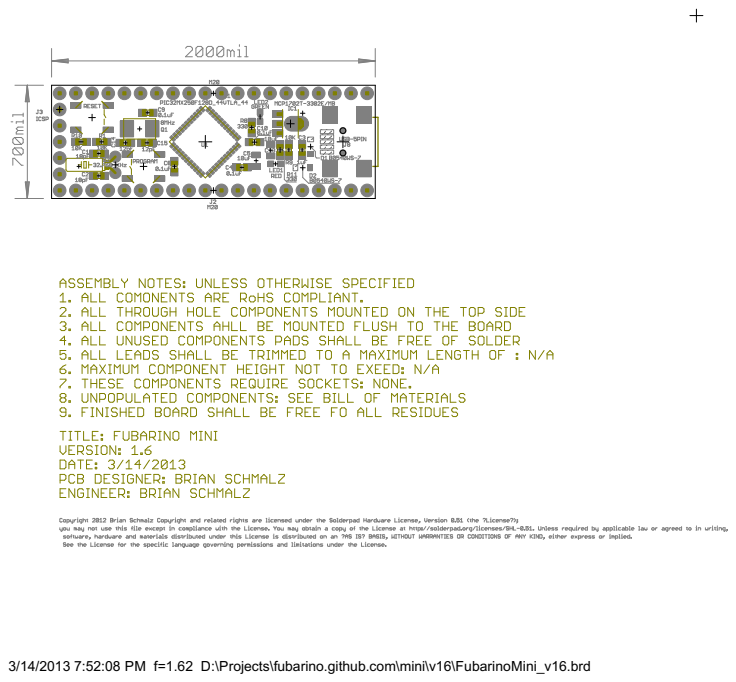
[picture p49: page 1]

3/14/2013 7:52:08 PM f=1.62 D:\Projects\fubarino.github.com\mini\v16\FubarinoMini_v16.brd
