fubarino/fubarino.github.com/mini/v15/FubarinoMini_v15_Assembly.pdf

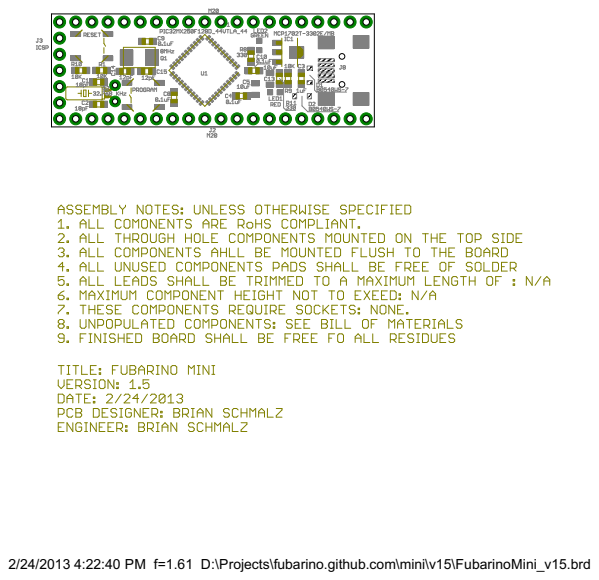
[picture p50: page 1]

2/24/2013 4:22:40 PM f=1.61 D:\Projects\fubarino.github.com\mini\v15\FubarinoMini_v15.brd
