fubarino/fubarino.github.com/accessories/FubarStep/FuabarStep_v11/FubarStep_v11_brd.pdf

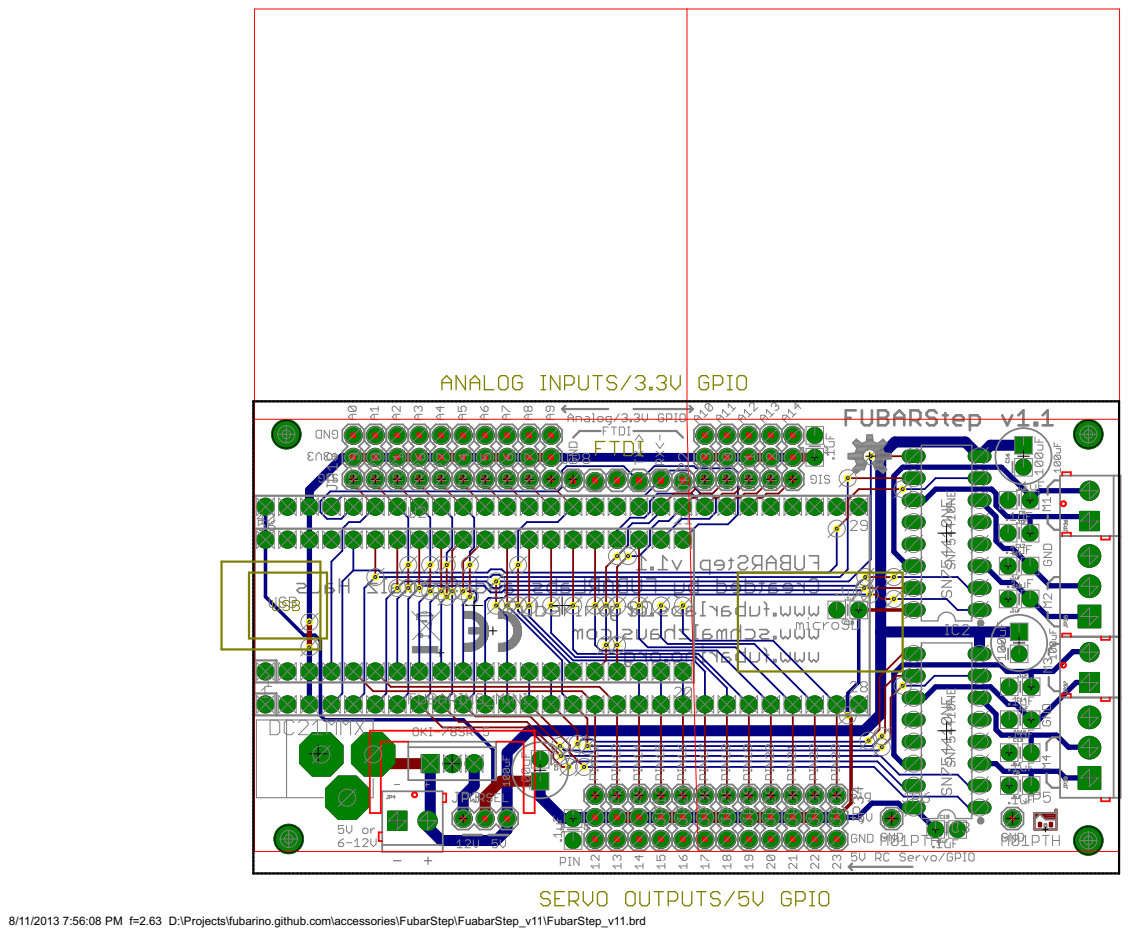
[picture p51: page 1]

8/11/2013 7:56:08 PM f=2.63 D:\Projects\fubarino.github.com\accessories\FubarStep\FuabarStep_v11\FubarStep_v11.brd
