fubarino/fubarino.github.com/accessories/FubarStep/FuabarStep_v10/FubarStep_v10_brd.pdf

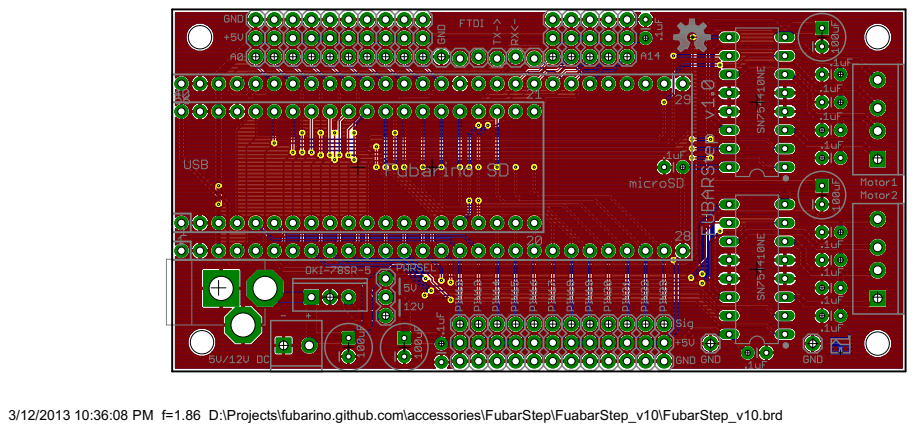
[picture p52: page 1]

3/12/2013 10:36:08 PM f=1.86 D:\Projects\fubarino.github.com\accessories\FubarStep\FuabarStep_v10\FubarStep_v10.brd
