fubarino/fubarino.github.com/mini/v11/FubarinoMini_v11_brd.pdf

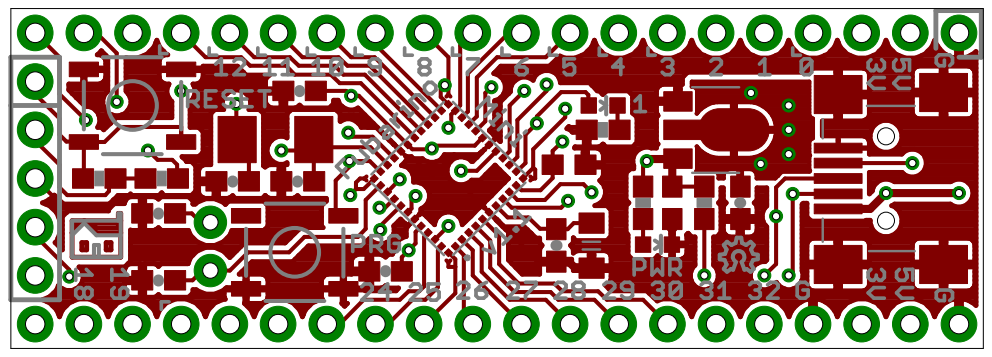
[picture p53: page 1]
