fubarino/fubarino.github.com/mini/v10/FubarinoMini_v10_brd.pdf

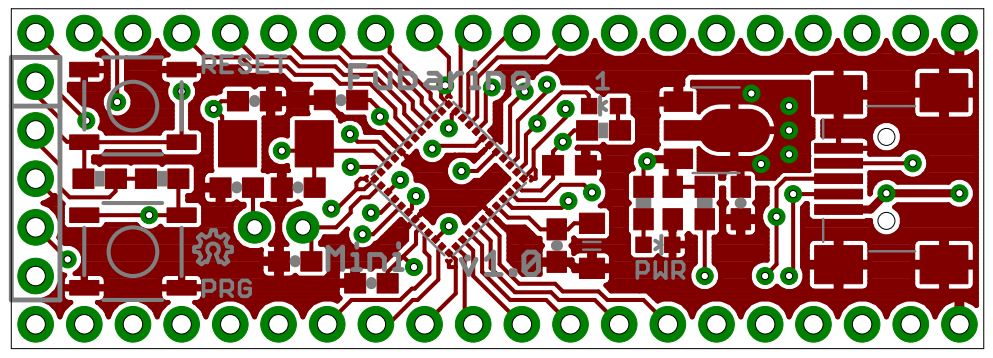
[picture p54: page 1]
