fubarino/fubarino.github.com/mini/v10/FubarinoMini_v10_brd_bot.pdf

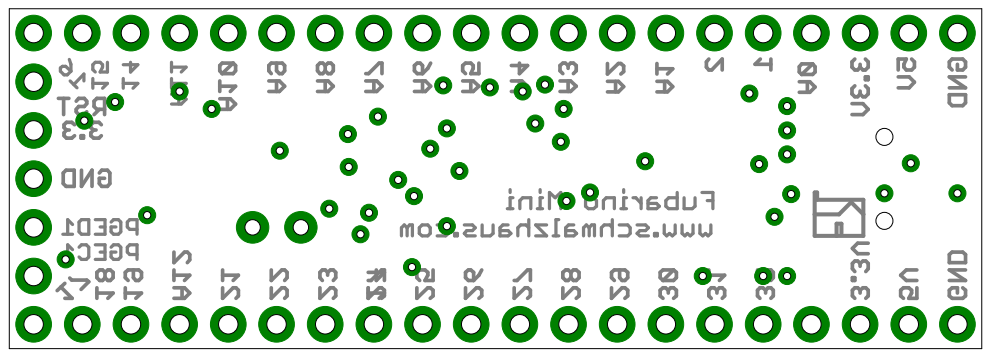
[picture p55: page 1]
