fubarino/fubarino.github.com/sd/v1.4/Fubarino_SD_v14_brd.pdf

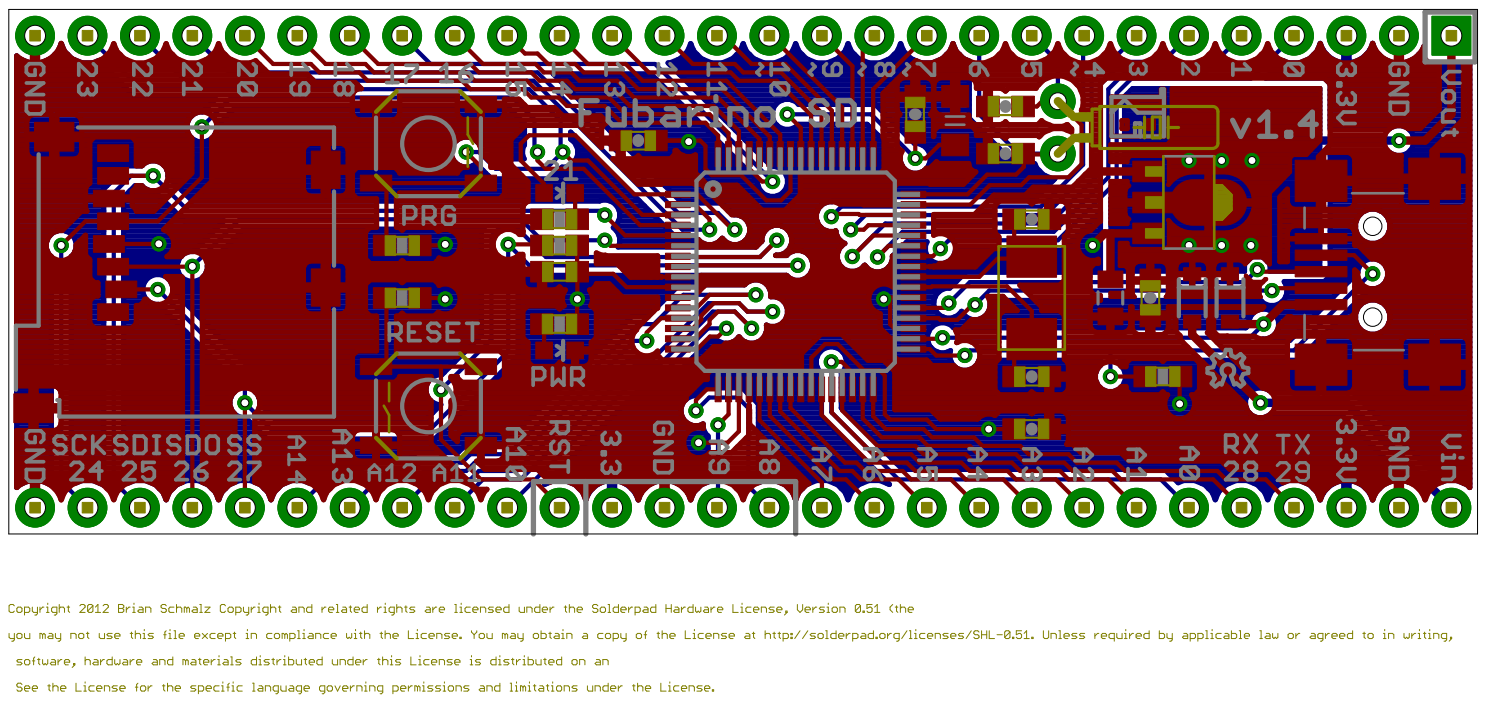
[picture p56: page 1]
