fubarino/fubarino.github.com/mini/v16/FromMicrochip/04-10064/04-10064/02-10064-Dr1.pdf

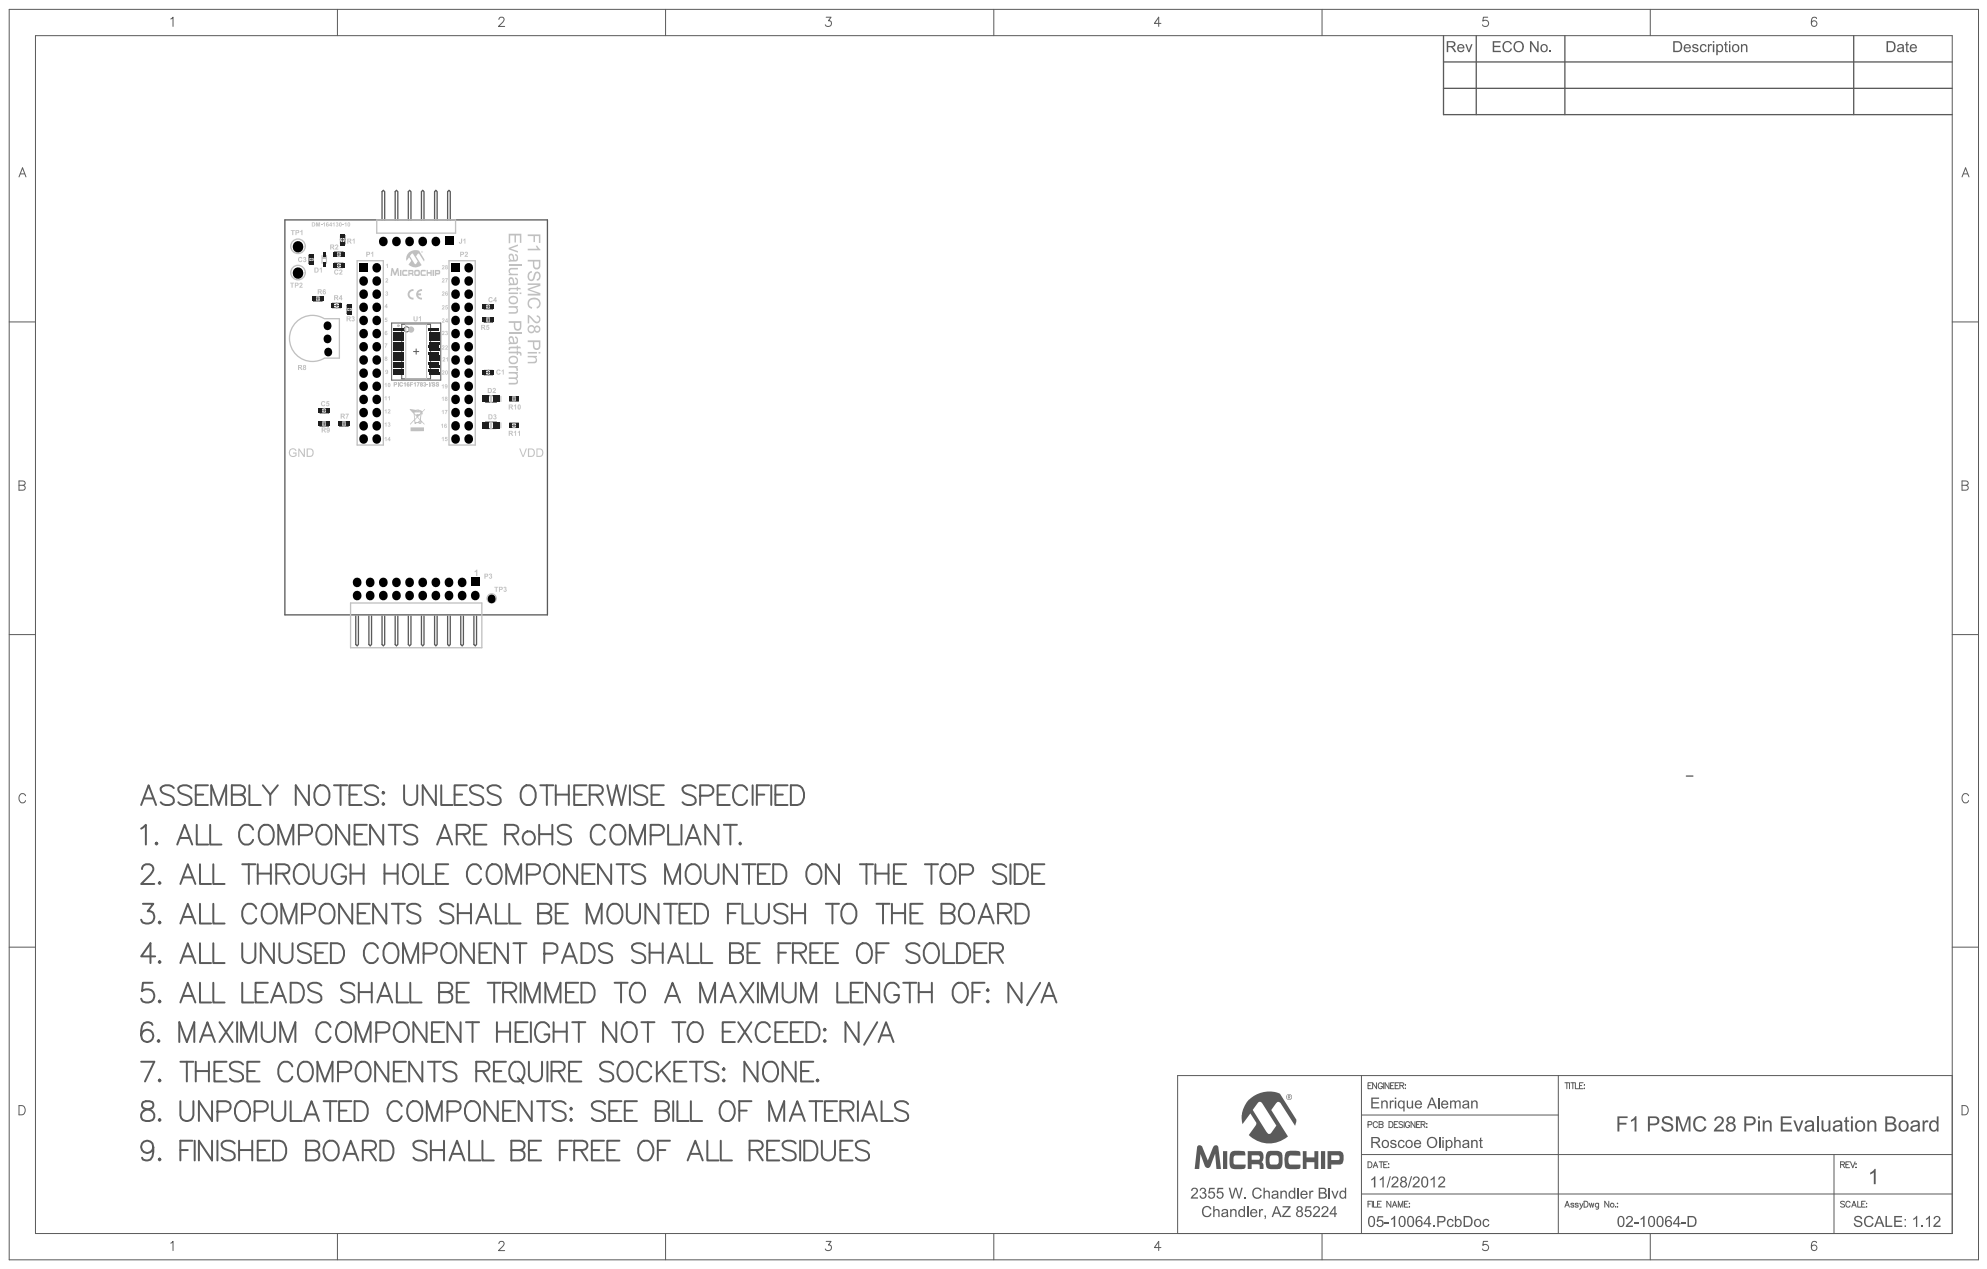
[picture p57: page 1]

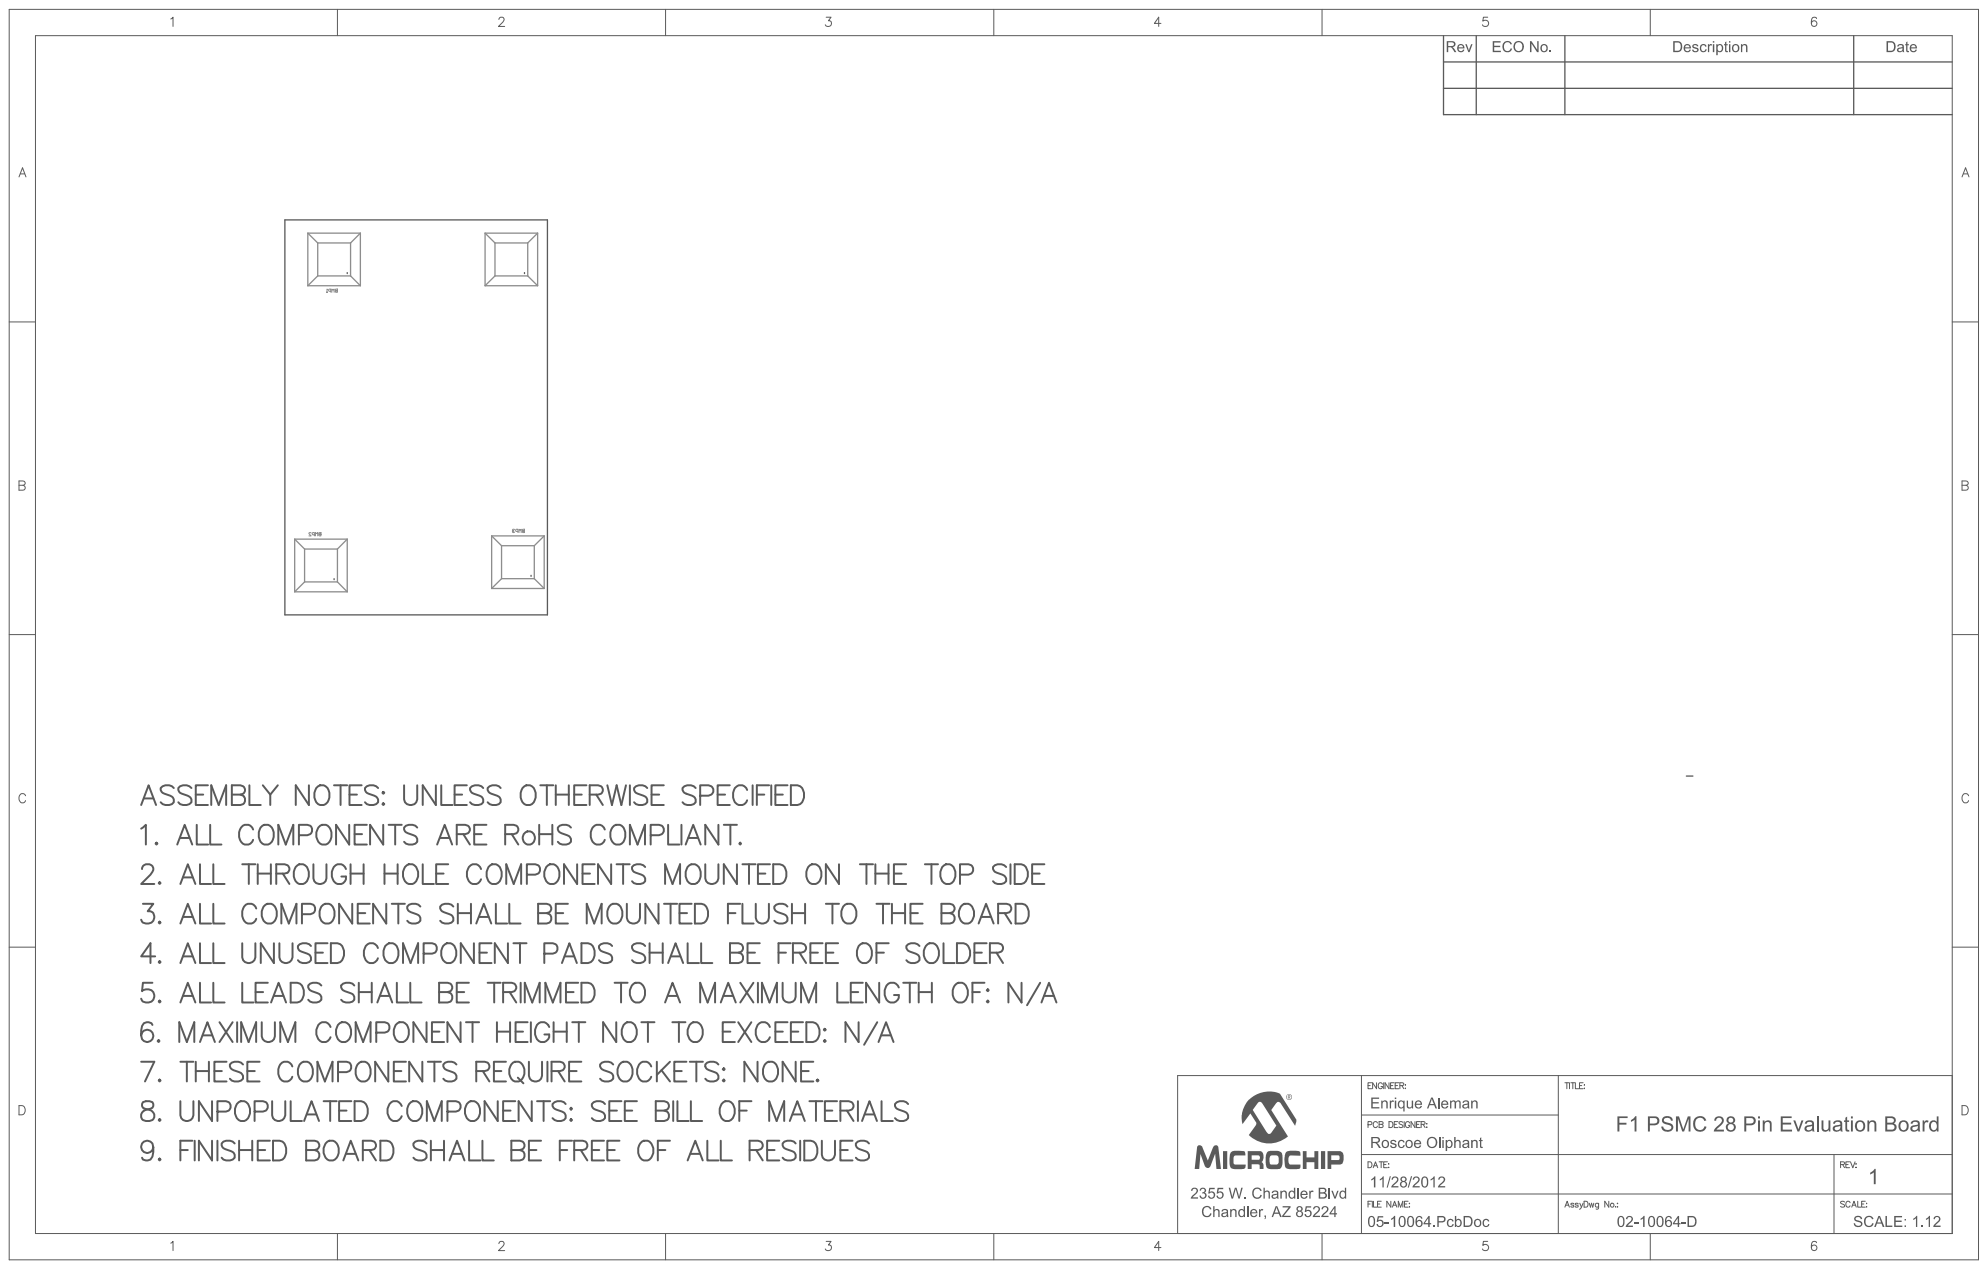
[picture p58: page 2]
