fubarino/fubarino.github.com/mini/v16/FromMicrochip/04-10064/04-10064/04-10064r1.pdf

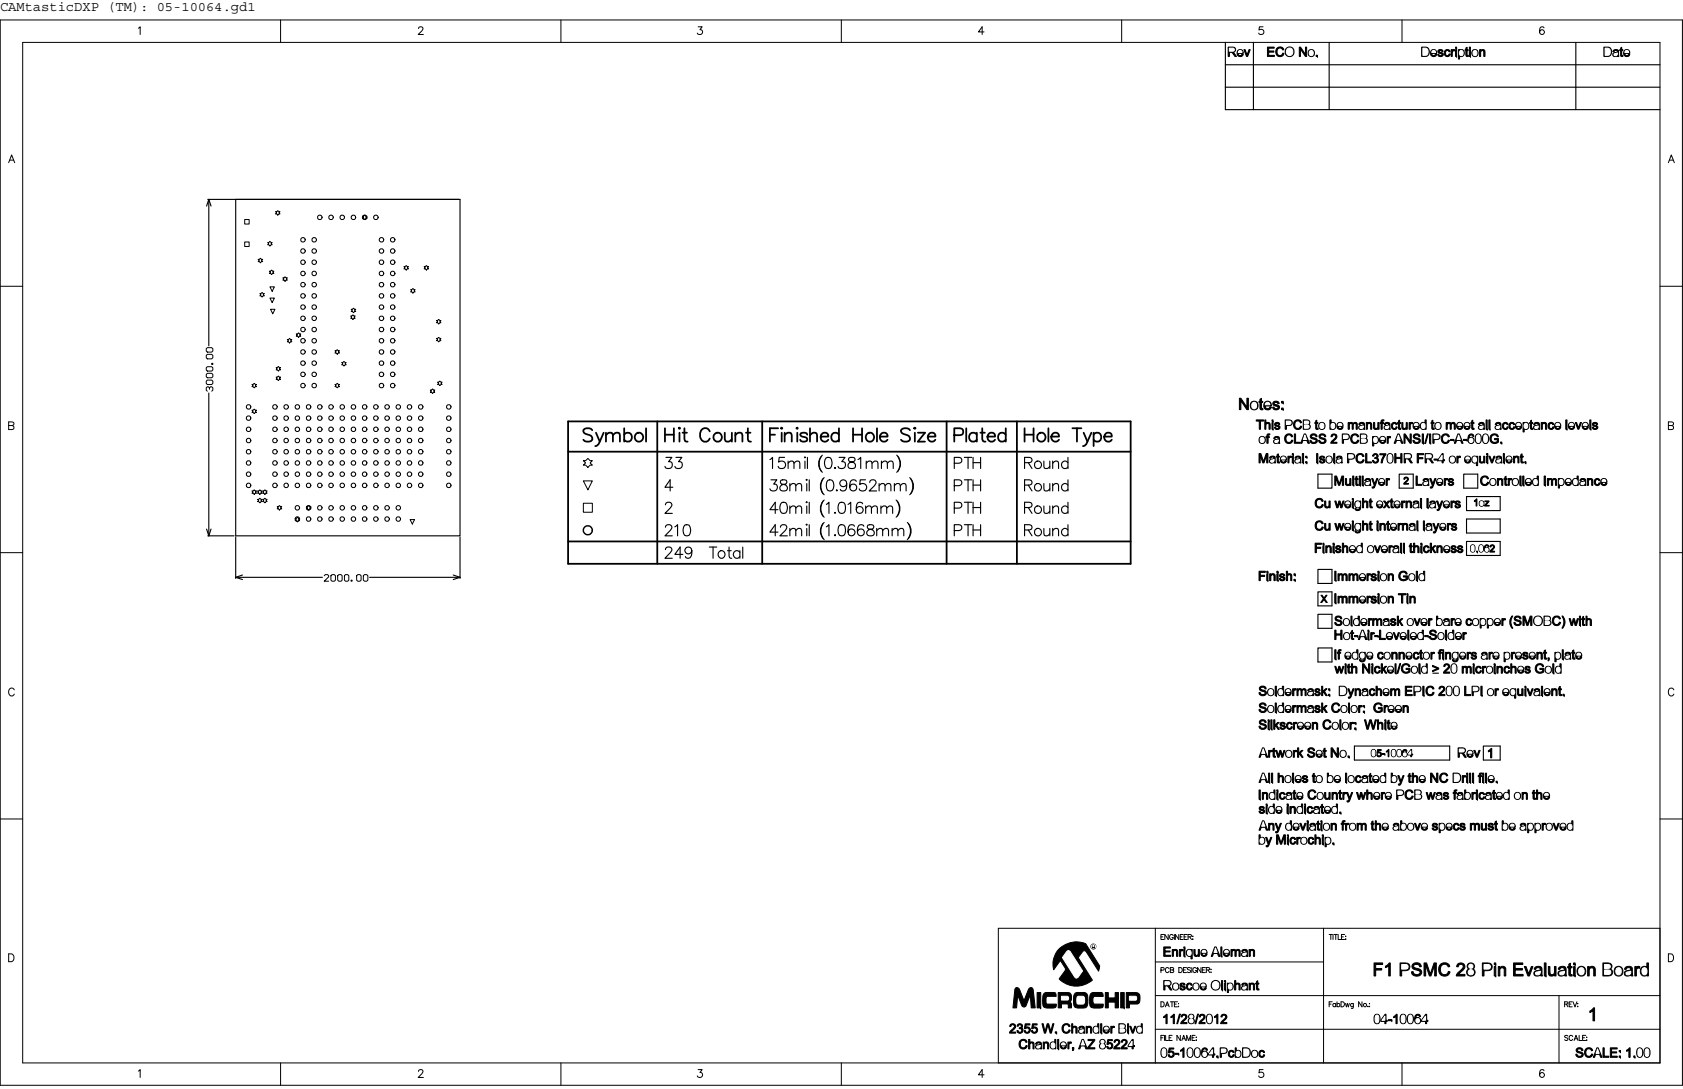
[picture p59: page 1]
CAMtasticDXP (TM): 05-10064.gd1
