fubarino/fubarino.github.com/mini/v11/FubarinoMini_v11.brd

## EAGLE design mini/v11/FubarinoMini_v11.brd (2013-01-29, an earlier design)

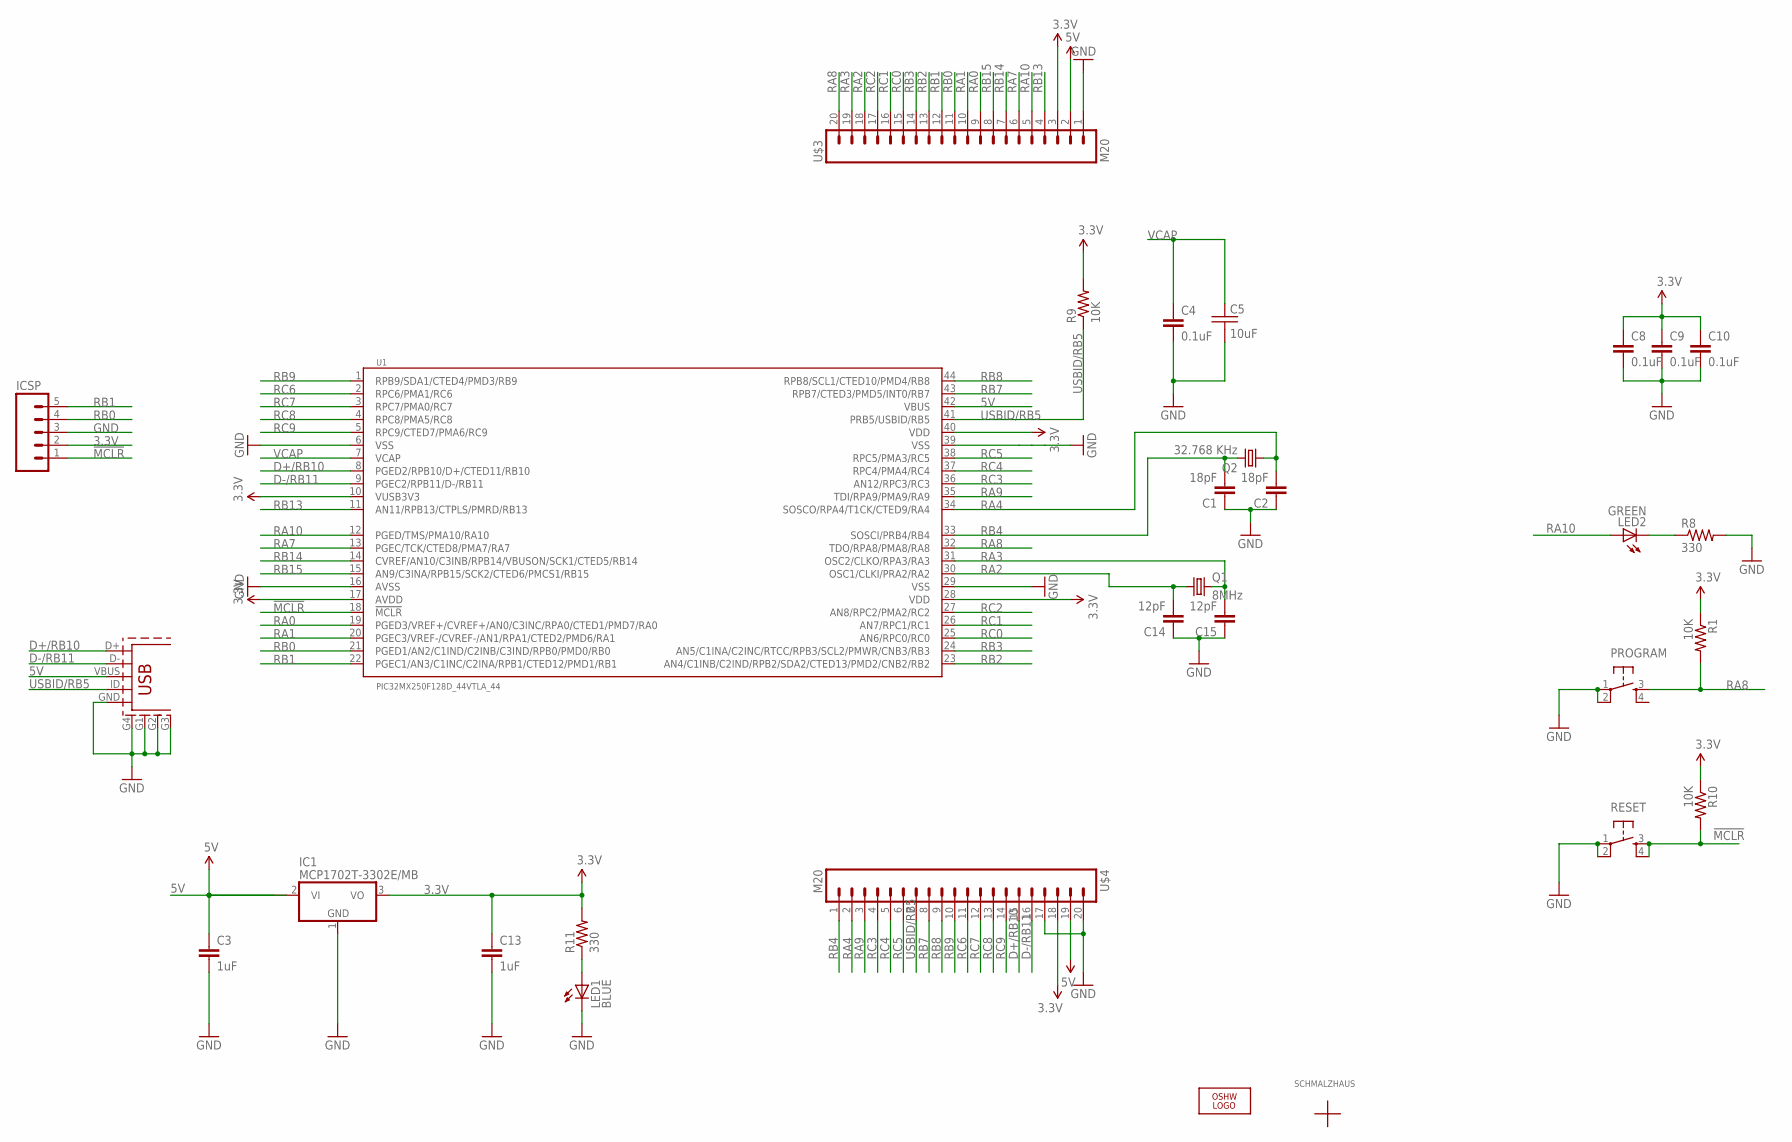
[picture p74: schematic FubarinoMini_v11.sch]

Parts:
C1, C2: 18pF; 0603-CAP
C3: 1uF; 0603-CAP
C4, C8, C9: 0.1uF; 0603-CAP
C5: 10uF; CAP_0805
C10: 0.1uF; 0603
C13: 1uF; 0603
C14, C15: 12pF; 0603-CAP
IC1: MCP1702T-3302E/MB; SOT89
ICSP: M05NOSLILK; 1X05_NOSILK
J8: USB_5PIN; USB-MINIB
LED1: BLUE; LED-0603
LED2: GREEN; LED-0603
LOGO1: OSHW_LOGO_8MILX0070-NT; OSHW_8X70_NOTEXT
PROGRAM: TAC_SWITCHSND; TACTILE_SWITCH_SMD
Q1: 8MHz; NX5032_5MM_3.2MM_CRYSTAL
Q2: 32.768 KHz; TC26H
R1, R9, R10: 10K; 0603-RES
R8, R11: 330; 0603-RES
RESET: TAC_SWITCHSND; TACTILE_SWITCH_SMD
U1: PIC32MX250F128D_44VTLA_44; VTLA_44
U$1: SCHMALZHAUSSCHMALZHAUS_SMALL; SCHMALZHAUS_SMALL
U$3, U$4: M20; 1X20_NO_PIN1

Connections:
3.3V: C8.1, C9.1, C10.1, C13.1, IC1.3 (VO), ICSP.2, R1.1, R9.2, R10.1, R11.2, U1.10 (VUSB3V3), U1.17 (AVDD), U1.28 (VDD), U1.40 (VDD), U$3.3, U$4.18
5V: C3.1, IC1.2 (VI), IC1.2@1 (VI1), J8.VBUS, U1.42 (VBUS), U$3.2, U$4.19
!MCLR!: ICSP.1, R10.2, RESET.3, RESET.4, U1.18 (!MCLR!)
D+/RB10: J8.D+, U1.8 (PGED2/RPB10/D+/CTED11/RB10), U$4.15
D-/RB11: J8.D-, U1.9 (PGEC2/RPB11/D-/RB11), U$4.16
GND: C1.1, C2.1, C3.2, C4.2, C5.2, C8.2, C9.2, C10.2, C13.2, C14.1, C15.1, IC1.1 (GND), ICSP.3, J8.G1, J8.G2, J8.G3, J8.G4 (SHIELD), J8.GND, LED1.C, PROGRAM.1, PROGRAM.2, R8.2, RESET.1, RESET.2, U1.6 (VSS), U1.16 (AVSS), U1.29 (VSS), U1.39 (VSS), U$3.1, U$4.17, U$4.20
unnamed: LED1.A, R11.1
unnamed: LED2.C, R8.1
RA0: U1.19 (PGED3/VREF+/CVREF+/AN0/C3INC/RPA0/CTED1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), U$3.9
RA1: U1.20 (PGEC3/VREF-/CVREF-/AN1/RPA1/CTED2/PMD6/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), U$3.10
RA2: C14.2, Q1.1, U1.30 (OSC1/CLKI/PRA2/RA2), U$3.18
RA3: C15.2, Q1.2, U1.31 (OSC2/CLKO/RPA3/RA3), U$3.19
RA4: C2.2, Q2.1, U1.34 (SOSCO/RPA4/T1CK/CTED9/RA4), U$4.2
RA7: U1.13 (PGEC/TCK/CTED8/PMA7/RA7), U$3.6
RA8: PROGRAM.3, R1.2, U1.32 (TDO/RPA8/PMA8/RA8), U$3.20
RA9: U1.35 (TDI/RPA9/PMA9/RA9), U$4.3
RA10: LED2.A, U1.12 (PGED/TMS/PMA10/RA10), U$3.5
RB0: ICSP.4, U1.21 (PGED1/AN2/C1IND/C2INB/C3IND/RPB0/PMD0/R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), U$3.11
RB1: ICSP.5, U1.22 (PGEC1/AN3/C1INC/C2INA/RPB1/CTED12/PMD1/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), U$3.12
RB2: U1.23 (AN4/C1INB/C2IND/RPB2/SDA2/CTED13/PMD2/C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), U$3.13
RB3: U1.24 (AN5/C1INA/C2INC/RTCC/RPB3/SCL2/PMWR/CNB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), U$3.14
RB4: C1.2, Q2.2, U1.33 (SOSCI/PRB4/RB4), U$4.1
RB7: U1.43 (RPB7/CTED3/PMD5/INT0/RB7), U$4.8
RB8: U1.44 (RPB8/SCL1/CTED10/PMD4/RB8), U$4.9
RB9: U1.1 (RPB9/SDA1/CTED4/PMD3/RB9), U$4.10
RB13: U1.11 (AN11/RPB13/CTPLS/PMRD/RB13), U$3.4
RB14: U1.14 (CVREF/AN10/C3INB/RPB14/VBUSON/SCK1/CTED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), U$3.7
RB15: U1.15 (AN9/C3INA/RPB15/SCK2/CTED6/PMCS1/RB15), U$3.8
RC0: U1.25 (AN6/RPC0/RC0), U$3.15
RC1: U1.26 (AN7/RPC1/RC1), U$3.16
RC2: U1.27 (AN8/RPC2/PMA2/RC2), U$3.17
RC3: U1.36 (AN12/RPC3/RC3), U$4.4
RC4: U1.37 (RPC4/PMA4/RC4), U$4.5
RC5: U1.38 (RPC5/PMA3/RC5), U$4.6
RC6: U1.2 (RPC6/PMA1/RC6), U$4.11
RC7: U1.3 (RPC7/PMA0/RC7), U$4.12
RC8: U1.4 (RPC8/PMA5/RC8), U$4.13
RC9: U1.5 (RPC9/CTED7/PMA6/RC9), U$4.14
USBID/RB5: J8.ID (USB_ID), R9.1, U1.41 (PRB5/USBID/RB5), U$4.7
VCAP: C4.1, C5.1, U1.7 (VCAP)

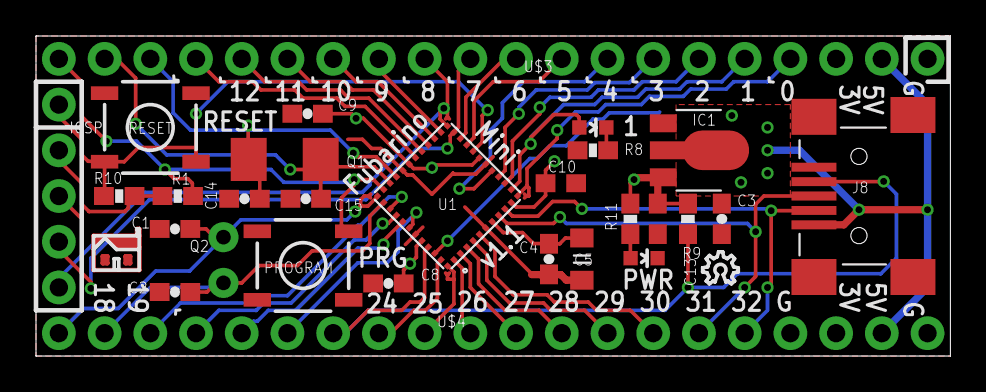
[picture p75: board FubarinoMini_v11.brd from above]

Board: 2 copper layers, 50.8 x 17.8 mm, 30 parts (0 on the bottom side), 40 nets.
