fubarino/fubarino.github.com/mini/v16/Pannel/FubarinoMini_v16_SeeedPannel.brd

## EAGLE design mini/v16/Pannel/FubarinoMini_v16_SeeedPannel.brd (2013-03-19, an earlier design)

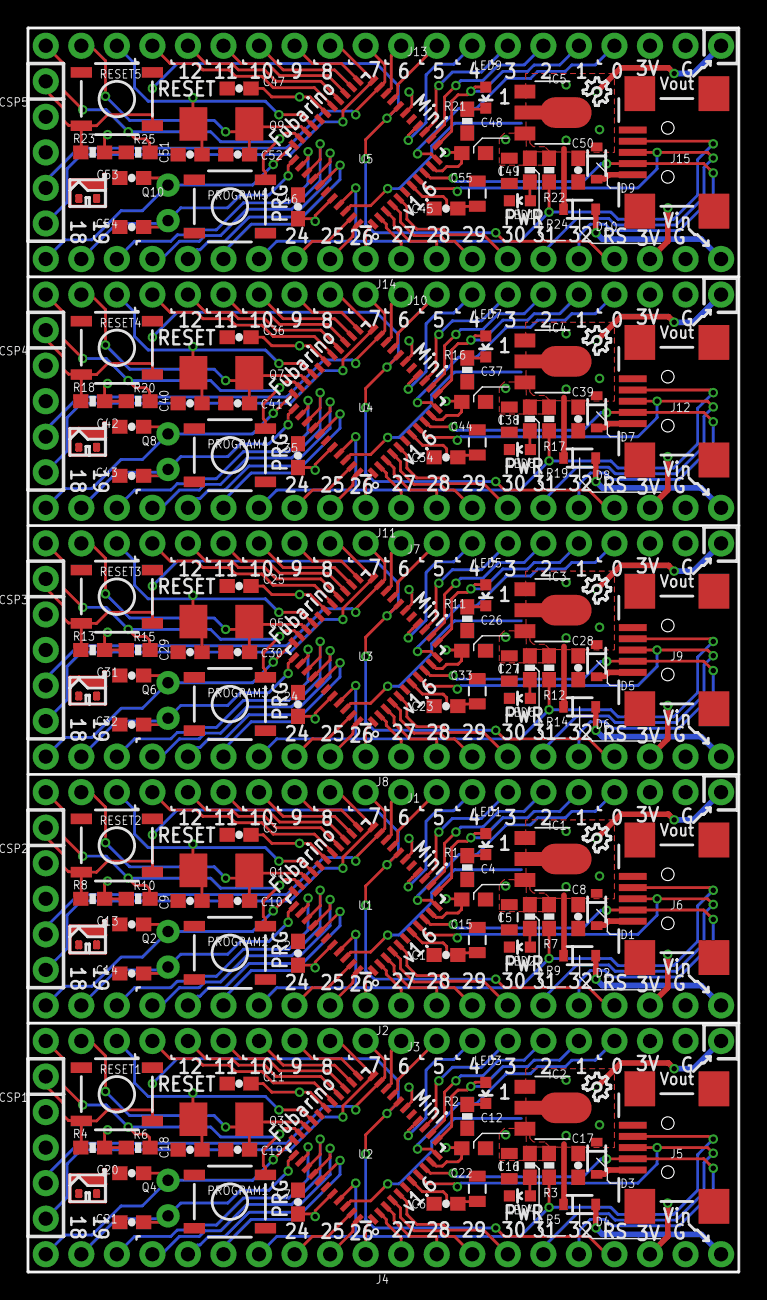
[picture p76: board FubarinoMini_v16_SeeedPannel.brd from above]

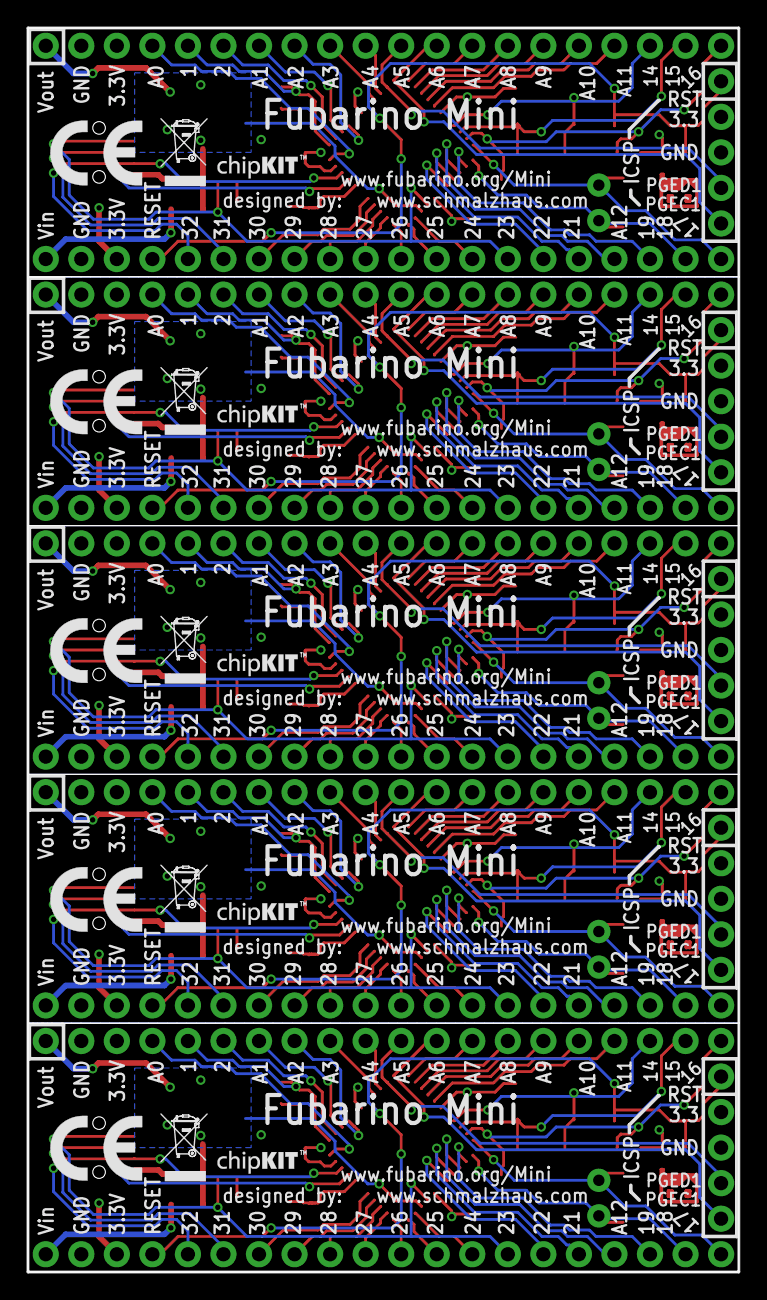
[picture p77: board FubarinoMini_v16_SeeedPannel.brd from below]

Board: 2 copper layers, 50.8 x 88.9 mm, 175 parts (15 on the bottom side), 210 nets.

Parts:
C1, C2, C3, C6, C7, C11, C23, C24, C25, C34, C35, C36, C45, C46, C47: 0.1uF; 0603-CAP
C4, C12, C26, C37, C48: 0.1uF; 0603
C5, C15, C16, C22, C27, C33, C38, C44, C49, C55: 10uF; 0805
C8, C17, C28, C39, C50: 1uF; 0603-CAP
C9, C10, C18, C19, C29, C30, C40, C41, C51, C52: 12pF; 0603-CAP
C13, C14, C20, C21, C31, C32, C42, C43, C53, C54: 18pF; 0603-CAP
D1, D2, D3, D4, D5, D6, D7, D8, D9, D10: B0540WS-7; SOD-323
IC1, IC2, IC3, IC4, IC5: MCP1702T-3302E/MB; SOT89
ICSP1, ICSP2, ICSP3, ICSP4, ICSP5: J3; 1X05_NOSILK
J1, J2, J3, J4, J7, J8, J10, J11, J13, J14: M20; 1X20_NO_PIN1
J5, J6, J9, J12, J15: USB-5PIN; USB-MINIB-5PIN-HIROSE-UX60-MB-5ST
LED1, LED3, LED5, LED7, LED9: GREEN; LED-0603
LED2, LED4, LED6, LED8, LED10: RED; LED-0603
LOGO1, LOGO2, LOGO3, LOGO4, LOGO5: OSHW_LOGO_8MILX0070-NT; OSHW_8X70_NOTEXT
PROGRAM1, PROGRAM2, PROGRAM3, PROGRAM4, PROGRAM5: TACTILE_SWITCH_SMD
Q1, Q3, Q5, Q7, Q9: 8MHz; NX5032_5MM_3.2MM_CRYSTAL
Q2, Q4, Q6, Q8, Q10: 32.768 KHz; TC26H
R1, R2, R5, R9, R11, R14, R16, R19, R21, R24: 330; 0603-RES
R3, R4, R6, R7, R8, R10, R12, R13, R15, R17, R18, R20, R22, R23, R25: 10K; 0603-RES
RESET1, RESET2, RESET3, RESET4, RESET5: TACTILE_SWITCH_SMD
U1, U2, U3, U4, U5: PIC32MX250F128D_44VTLA_44; QFN-44-8X8-NOPAD
U$1, U$5, U$9, U$13, U$17: SCHMALZHAUSSCHMALZHAUS_SMALL; SCHMALZHAUS_SMALL
U$2, U$6, U$10, U$14, U$18: CE_MARK5MM; CE_5MM
U$3, U$7, U$11, U$15, U$19: ROSH_GARBAGE; ROHS_GARBAGE_5MM
U$4, U$8, U$12, U$16, U$20: CHIPKIT2MM; CHIPKIT_2MM

Connections:
3.3V1: C7.1, C11.1, C12.1, C16.1, IC2.3, ICSP1.2, J3.3, J4.18, R3.2, R4.1, R5.2, R6.1, U2.10, U2.17, U2.28, U2.40
3.3V2: C2.1, C3.1, C4.1, C5.1, IC1.3, ICSP2.2, J1.3, J2.18, R7.2, R8.1, R9.2, R10.1, U1.10, U1.17, U1.28, U1.40
3.3V3: C24.1, C25.1, C26.1, C27.1, IC3.3, ICSP3.2, J7.3, J8.18, R12.2, R13.1, R14.2, R15.1, U3.10, U3.17, U3.28, U3.40
3.3V4: C35.1, C36.1, C37.1, C38.1, IC4.3, ICSP4.2, J10.3, J11.18, R17.2, R18.1, R19.2, R20.1, U4.10, U4.17, U4.28, U4.40
3.3V5: C46.1, C47.1, C48.1, C49.1, IC5.3, ICSP5.2, J13.3, J14.18, R22.2, R23.1, R24.2, R25.1, U5.10, U5.17, U5.28, U5.40
5V1: C17.1, D3.1, D4.1, IC2.2, IC2.2@1, J3.1, U2.42
5V2: C8.1, D1.1, D2.1, IC1.2, IC1.2@1, J1.1, U1.42
5V3: C28.1, D5.1, D6.1, IC3.2, IC3.2@1, J7.1, U3.42
5V4: C39.1, D7.1, D8.1, IC4.2, IC4.2@1, J10.1, U4.42
5V5: C50.1, D9.1, D10.1, IC5.2, IC5.2@1, J13.1, U5.42
!MCLR!1: ICSP1.1, J4.17, R4.2, RESET1.3, RESET1.4, U2.18
!MCLR!2: ICSP2.1, J2.17, R8.2, RESET2.3, RESET2.4, U1.18
!MCLR!3: ICSP3.1, J8.17, R13.2, RESET3.3, RESET3.4, U3.18
!MCLR!4: ICSP4.1, J11.17, R18.2, RESET4.3, RESET4.4, U4.18
!MCLR!5: ICSP5.1, J14.17, R23.2, RESET5.3, RESET5.4, U5.18
D+/RB1: J4.15, J5.D+, U2.8
D+/RB2: J2.15, J6.D+, U1.8
D+/RB3: J8.15, J9.D+, U3.8
D+/RB4: J11.15, J12.D+, U4.8
D+/RB5: J14.15, J15.D+, U5.8
D-/RB1: J4.16, J5.D-, U2.9
D-/RB2: J2.16, J6.D-, U1.9
D-/RB3: J8.16, J9.D-, U3.9
D-/RB4: J11.16, J12.D-, U4.9
D-/RB5: J14.16, J15.D-, U5.9
GND1: C6.2, C7.2, C11.2, C12.2, C16.2, C17.2, C18.1, C19.1, C20.1, C21.1, C22.2, IC2.1, ICSP1.3, J3.2, J4.19, J5.GND, J5.MTN1, J5.MTN2, J5.MTN3, J5.MTN4, LED4.C, PROGRAM1.1, PROGRAM1.2, R2.2, RESET1.1, RESET1.2, U2.6, U2.16, U2.29, U2.39
GND2: C1.2, C2.2, C3.2, C4.2, C5.2, C8.2, C9.1, C10.1, C13.1, C14.1, C15.2, IC1.1, ICSP2.3, J1.2, J2.19, J6.GND, J6.MTN1, J6.MTN2, J6.MTN3, J6.MTN4, LED2.C, PROGRAM2.1, PROGRAM2.2, R1.2, RESET2.1, RESET2.2, U1.6, U1.16, U1.29, U1.39
GND3: C23.2, C24.2, C25.2, C26.2, C27.2, C28.2, C29.1, C30.1, C31.1, C32.1, C33.2, IC3.1, ICSP3.3, J7.2, J8.19, J9.GND, J9.MTN1, J9.MTN2, J9.MTN3, J9.MTN4, LED6.C, PROGRAM3.1, PROGRAM3.2, R11.2, RESET3.1, RESET3.2, U3.6, U3.16, U3.29, U3.39
GND4: C34.2, C35.2, C36.2, C37.2, C38.2, C39.2, C40.1, C41.1, C42.1, C43.1, C44.2, IC4.1, ICSP4.3, J10.2, J11.19, J12.GND, J12.MTN1, J12.MTN2, J12.MTN3, J12.MTN4, LED8.C, PROGRAM4.1, PROGRAM4.2, R16.2, RESET4.1, RESET4.2, U4.6, U4.16, U4.29, U4.39
GND5: C45.2, C46.2, C47.2, C48.2, C49.2, C50.2, C51.1, C52.1, C53.1, C54.1, C55.2, IC5.1, ICSP5.3, J13.2, J14.19, J15.GND, J15.MTN1, J15.MTN2, J15.MTN3, J15.MTN4, LED10.C, PROGRAM5.1, PROGRAM5.2, R21.2, RESET5.1, RESET5.2, U5.6, U5.16, U5.29, U5.39
unnamed: LED3.C, R2.1
unnamed: LED4.A, R5.1
unnamed: LED1.C, R1.1
unnamed: LED2.A, R9.1
unnamed: LED5.C, R11.1
unnamed: LED6.A, R14.1
unnamed: LED7.C, R16.1
unnamed: LED8.A, R19.1
unnamed: LED9.C, R21.1
unnamed: LED10.A, R24.1
RA1: C10.2, J1.19, Q1.2, U1.31
RA2: C9.2, J1.18, Q1.1, U1.30
RA3: J2.3, U1.35
RA4: J1.20, PROGRAM2.3, R10.2, U1.32
RA5: C19.2, J3.19, Q3.2, U2.31
RA6: C18.2, J3.18, Q3.1, U2.30
RA7: J1.5, LED1.A, U1.12
RA8: J1.6, U1.13
RA9: J1.9, U1.19
RA10: J1.10, U1.20
RA11: J4.3, U2.35
RA12: J3.20, PROGRAM1.3, R6.2, U2.32
RA13: J3.5, LED3.A, U2.12
RA14: J3.6, U2.13
RA15: J3.9, U2.19
RA16: J3.10, U2.20
RA17: C21.2, J4.2, Q4.1, U2.34
RA18: C14.2, J2.2, Q2.1, U1.34
RA19: C30.2, J7.19, Q5.2, U3.31
RA20: C29.2, J7.18, Q5.1, U3.30
RA21: J8.3, U3.35
RA22: J7.20, PROGRAM3.3, R15.2, U3.32
RA23: J7.5, LED5.A, U3.12
RA24: J7.6, U3.13
RA25: J7.9, U3.19
RA26: J7.10, U3.20
RA27: C32.2, J8.2, Q6.1, U3.34
RA28: C41.2, J10.19, Q7.2, U4.31
RA29: C40.2, J10.18, Q7.1, U4.30
RA30: J11.3, U4.35
RA31: J10.20, PROGRAM4.3, R20.2, U4.32
RA32: J10.5, LED7.A, U4.12
RA33: J10.6, U4.13
RA34: J10.9, U4.19
RA35: J10.10, U4.20
RA36: C43.2, J11.2, Q8.1, U4.34
RA37: C52.2, J13.19, Q9.2, U5.31
RA38: C51.2, J13.18, Q9.1, U5.30
RA39: J14.3, U5.35
RA40: J13.20, PROGRAM5.3, R25.2, U5.32
RA41: J13.5, LED9.A, U5.12
RA42: J13.6, U5.13
RA43: J13.9, U5.19
RA44: J13.10, U5.20
RA45: C54.2, J14.2, Q10.1, U5.34
RB1: J2.9, U1.44
RB2: J2.10, U1.1
RB3: J1.4, U1.11
RB4: J1.7, U1.14
RB5: J4.9, U2.44
RB6: J4.10, U2.1
RB7: J1.8, U1.15
RB8: ICSP2.5, J1.12, U1.22
RB9: ICSP2.4, J1.11, U1.21
RB10: J3.4, U2.11
RB11: J3.7, U2.14
RB12: J3.8, U2.15
RB13: J2.8, U1.43
RB14: J1.14, U1.24
RB15: J1.13, U1.23
RB16: ICSP1.5, J3.12, U2.22
RB17: ICSP1.4, J3.11, U2.21
RB18: J4.8, U2.43
RB19: J3.14, U2.24
RB20: J3.13, U2.23
RB21: C20.2, J4.1, Q4.2, U2.33
RB22: C13.2, J2.1, Q2.2, U1.33
RB23: J8.9, U3.44
RB24: J8.10, U3.1
RB25: J7.4, U3.11
RB26: J7.7, U3.14
RB27: J7.8, U3.15
RB28: ICSP3.5, J7.12, U3.22
RB29: ICSP3.4, J7.11, U3.21
RB30: J8.8, U3.43
RB31: J7.14, U3.24
RB32: J7.13, U3.23
RB33: C31.2, J8.1, Q6.2, U3.33
RB34: J11.9, U4.44
RB35: J11.10, U4.1
RB36: J10.4, U4.11
RB37: J10.7, U4.14
RB38: J10.8, U4.15
RB39: ICSP4.5, J10.12, U4.22
RB40: ICSP4.4, J10.11, U4.21
RB41: J11.8, U4.43
RB42: J10.14, U4.24
RB43: J10.13, U4.23
RB44: C42.2, J11.1, Q8.2, U4.33
RB45: J14.9, U5.44
RB46: J14.10, U5.1
RB47: J13.4, U5.11
RB48: J13.7, U5.14
RB49: J13.8, U5.15
RB50: ICSP5.5, J13.12, U5.22
RB51: ICSP5.4, J13.11, U5.21
RB52: J14.8, U5.43
RB53: J13.14, U5.24
RB54: J13.13, U5.23
RB55: C53.2, J14.1, Q10.2, U5.33
RC1: J2.6, U1.38
RC2: J2.5, U1.37
RC3: J2.4, U1.36
RC4: J1.17, U1.27
RC5: J1.16, U1.26
RC6: J1.15, U1.25
RC7: J2.11, U1.2
RC8: J2.12, U1.3
RC9: J2.13, U1.4
RC10: J4.6, U2.38
RC11: J4.5, U2.37
RC12: J4.4, U2.36
RC13: J3.17, U2.27
RC14: J3.16, U2.26
RC15: J3.15, U2.25
RC16: J4.11, U2.2
RC17: J4.12, U2.3
RC18: J4.13, U2.4
RC19: J4.14, U2.5
RC20: J2.14, U1.5
RC21: J8.6, U3.38
RC22: J8.5, U3.37
RC23: J8.4, U3.36
RC24: J7.17, U3.27
RC25: J7.16, U3.26
RC26: J7.15, U3.25
RC27: J8.11, U3.2
RC28: J8.12, U3.3
RC29: J8.13, U3.4
RC30: J8.14, U3.5
RC31: J11.6, U4.38
RC32: J11.5, U4.37
RC33: J11.4, U4.36
RC34: J10.17, U4.27
RC35: J10.16, U4.26
RC36: J10.15, U4.25
RC37: J11.11, U4.2
RC38: J11.12, U4.3
RC39: J11.13, U4.4
RC40: J11.14, U4.5
RC41: J14.6, U5.38
RC42: J14.5, U5.37
RC43: J14.4, U5.36
RC44: J13.17, U5.27
RC45: J13.16, U5.26
RC46: J13.15, U5.25
RC47: J14.11, U5.2
RC48: J14.12, U5.3
RC49: J14.13, U5.4
RC50: J14.14, U5.5
USBID/RB1: J4.7, J5.ID, R3.1, U2.41
USBID/RB2: J2.7, J6.ID, R7.1, U1.41
USBID/RB3: J8.7, J9.ID, R12.1, U3.41
USBID/RB4: J11.7, J12.ID, R17.1, U4.41
USBID/RB5: J14.7, J15.ID, R22.1, U5.41
VBUS1: D3.2, J5.VBUS
VBUS2: D1.2, J6.VBUS
VBUS3: D5.2, J9.VBUS
VBUS4: D7.2, J12.VBUS
VBUS5: D9.2, J15.VBUS
VCAP1: C6.1, C22.1, U2.7
VCAP2: C1.1, C15.1, U1.7
VCAP3: C23.1, C33.1, U3.7
VCAP4: C34.1, C44.1, U4.7
VCAP5: C45.1, C55.1, U5.7
VIN1: D4.2, J4.20
VIN2: D2.2, J2.20
VIN3: D6.2, J8.20
VIN4: D8.2, J11.20
VIN5: D10.2, J14.20
